epccs/RPUno/Hardware/Evaluation/RPUno^5+K3^1+RPUadpt^4_wValvesPvBat.jpg

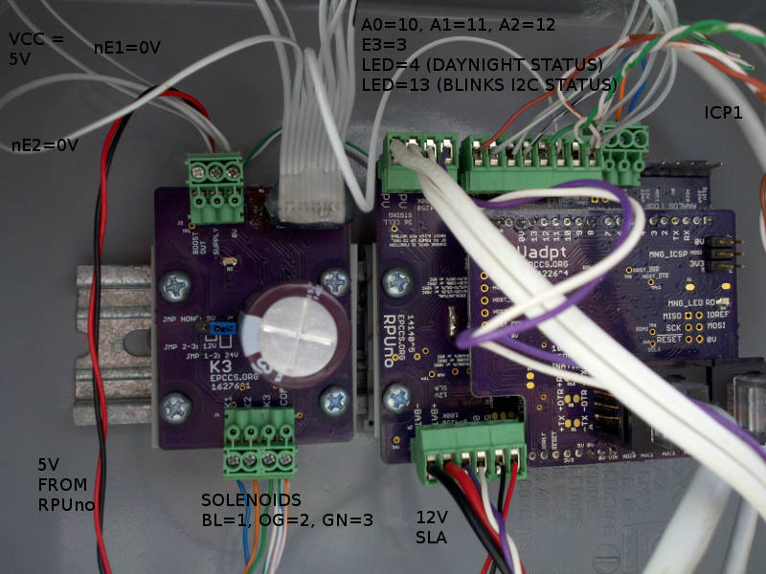
Hardware/Evaluation/RPUno^5+K3^1+RPUadpt^4_wValvesPvBat.jpg
