epccs/RPUno/Alternat/Setup/AuxilaryWiring.sch

## EAGLE design Alternat/Setup/AuxilaryWiring.sch (2018-12-21)

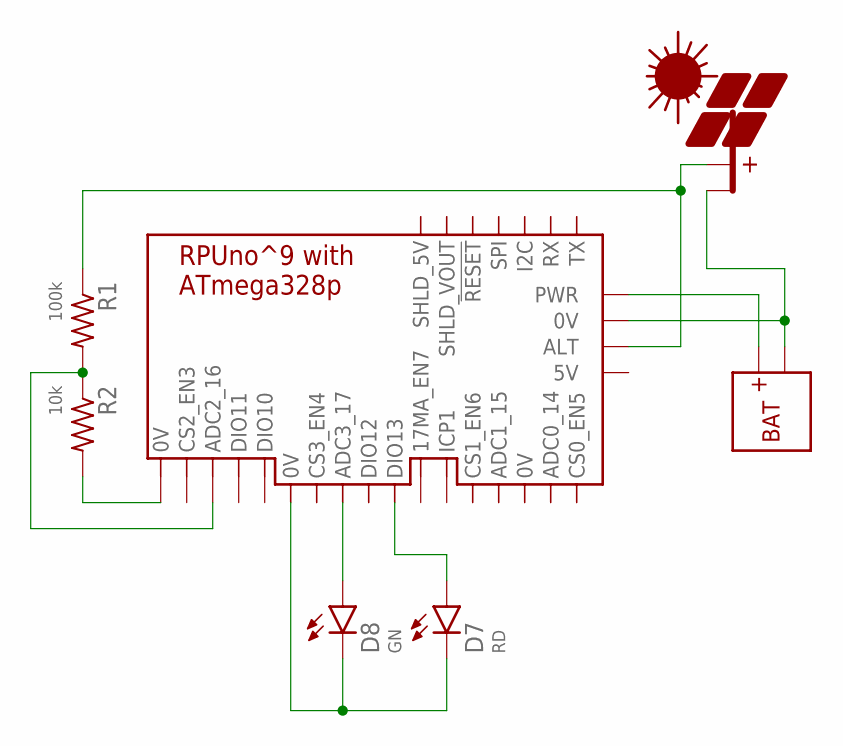
[picture p53: schematic AuxilaryWiring.sch]

Parts:
BM1: RPUNO; NA-30
D7: RD; LED5MM
D8: GN; LED5MM
PV4: PV; NA-30
R1: 100k; C0805(2012)
R2: 10k; C0805(2012)
U$7: BAT; NA-30

Connections:
unnamed: BM1.27 (0V), R2.2
unnamed: BM1.13 (ADC2_16), R1.2, R2.1
unnamed: BM1.18 (DIO13), D7.A
unnamed: BM1.28 (0V), D7.K, D8.K
unnamed: BM1.16 (ADC3_17), D8.A
unnamed: BM1.8 (PWR), U$7.1 (+BAT)
unnamed: BM1.9 (0V), PV4.2 (-PV), U$7.2 (-BAT)
unnamed: BM1.20 (ALT), PV4.1 (+PV), R1.1
