epccs/RPUno/DayNight/Setup/LightSensorWiring.sch

## EAGLE design DayNight/Setup/LightSensorWiring.sch (2018-12-10)

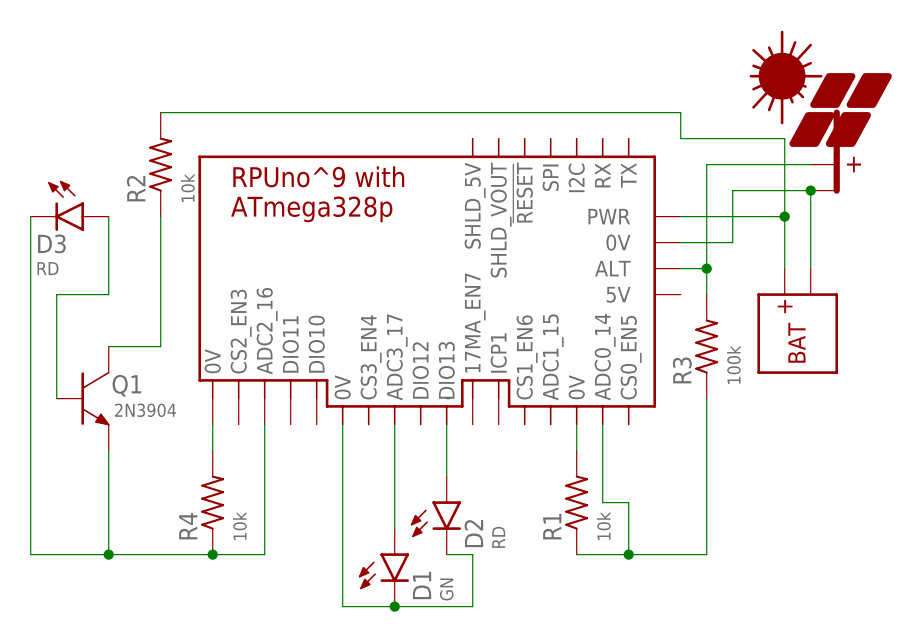
[picture p54: schematic LightSensorWiring.sch]

Parts:
BM1: RPUNO; NA-30
D1: GN; LED5MM
D2, D3: RD; LED5MM
PV4: PV; NA-30
Q1: 2N3904; SOT23
R1, R2, R4: 10k; C0805(2012)
R3: 100k; C0805(2012)
U$7: BAT; NA-30

Connections:
0V: BM1.9 (0V), PV4.2 (-PV), U$7.2 (-BAT)
unnamed: BM1.8 (PWR), R2.2, U$7.1 (+BAT)
unnamed: BM1.26 (0V), R1.2
unnamed: BM1.28 (0V), D1.K, D2.K
unnamed: D3.A, Q1.B
unnamed: BM1.13 (ADC2_16), D3.K, Q1.E, R4.1
unnamed: BM1.11 (ADC0_14), R1.1, R3.1
unnamed: Q1.C, R2.1
unnamed: BM1.27 (0V), R4.2
unnamed: BM1.18 (DIO13), D2.A
unnamed: BM1.16 (ADC3_17), D1.A
unnamed: BM1.20 (ALT), PV4.1 (+PV), R3.2
