epccs/RPUno/Hardware/Design/MultiDrop.sch

## EAGLE design Hardware/Design/MultiDrop.sch (2018-05-22)

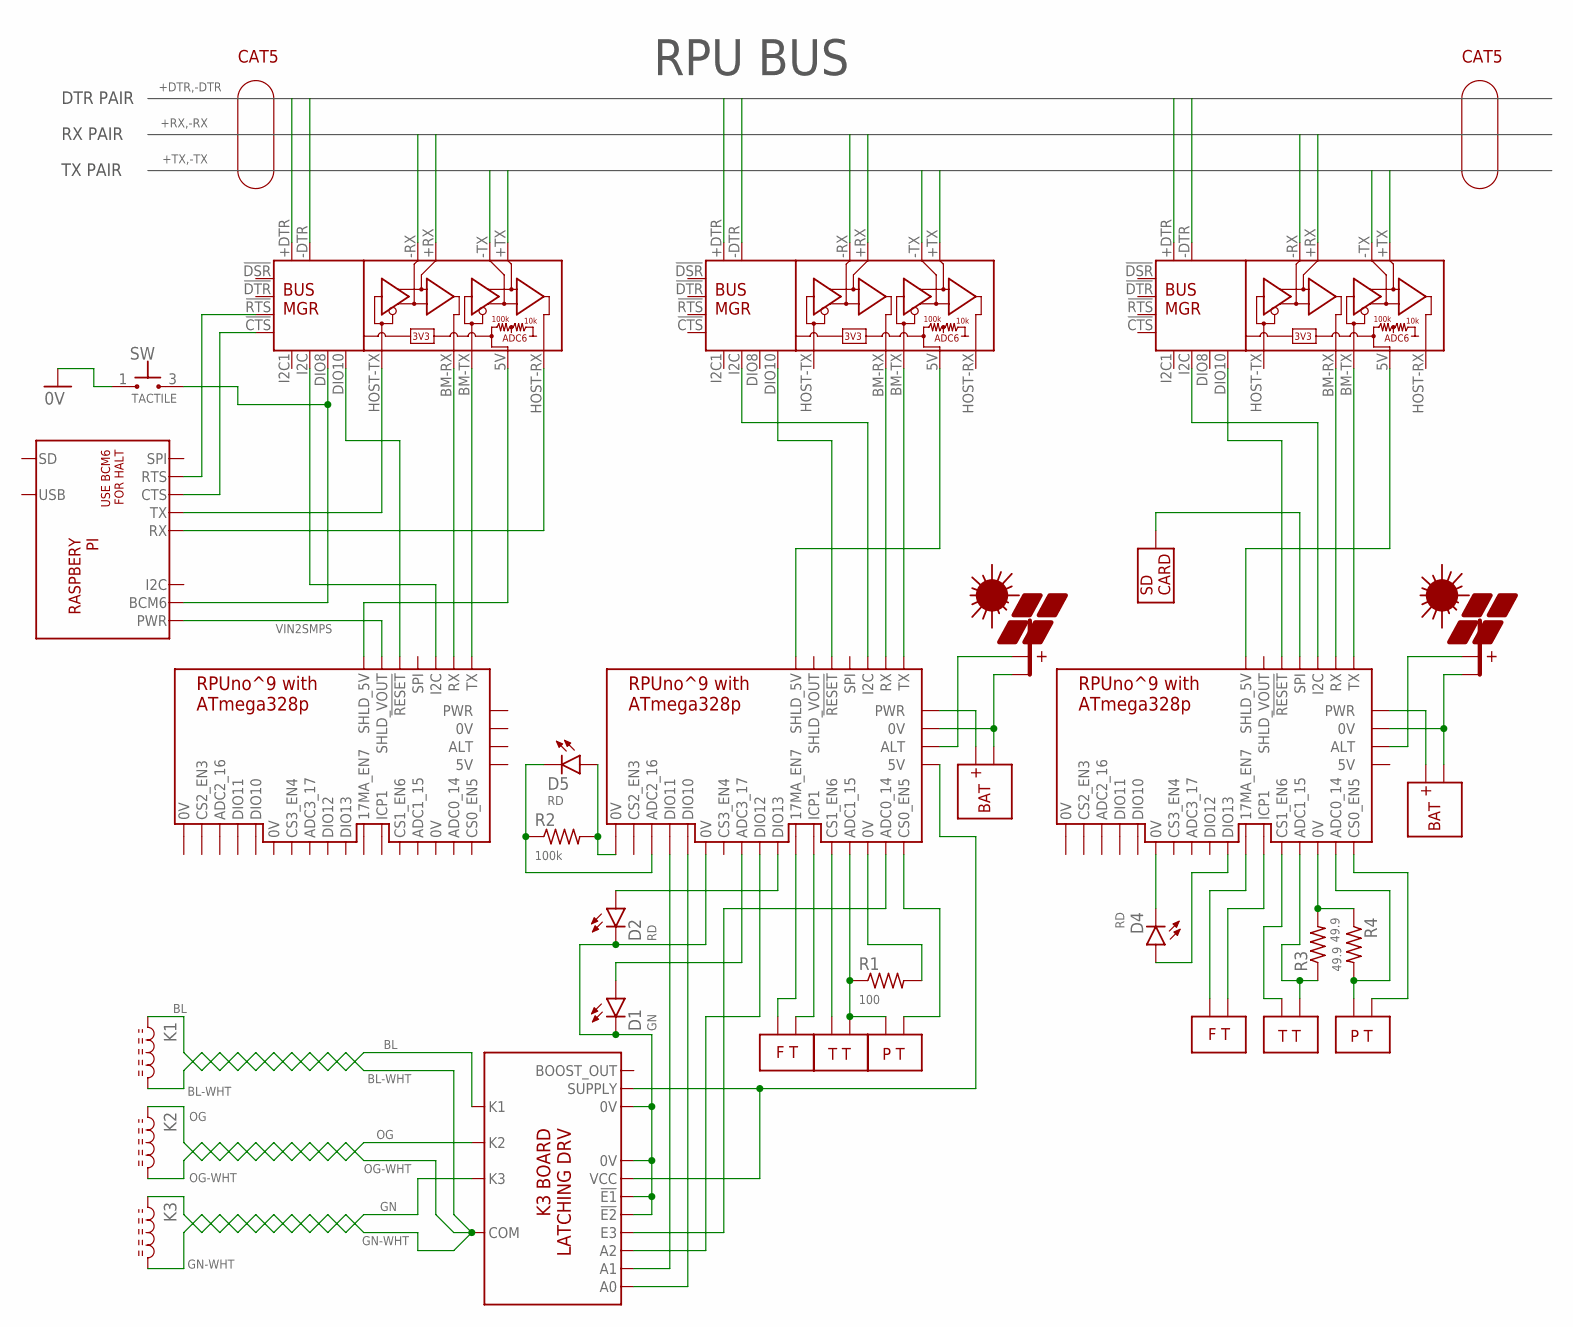
[picture p55: schematic MultiDrop.sch]

Parts:
BM1, BM2, BM3: RPUNO; NA-30
D1: GN; LED5MM
D2, D4, D5: RD; LED5MM
K1, K2, K3: L0805; C0805(2012)
PV2, PV4: PV; NA-30
R1: 100; C0805(2012)
R2: 100k; C0805(2012)
R3, R4: 49.9; C0805(2012)
SD2: SD; NA-30
SW: TACTILE; KS11
U$1, U$2, U$3: BUS_MGR; WITH_RPU_NAMES
U$4: K3; NA-30
U$5, U$12: FT; NA-30
U$6, U$10: TT; NA-30
U$7, U$9: BAT; NA-30
U$8, U$11: PT; NA-30
U$13: PI; NA-30

Connections:
0V: SW.1
+DTR: U$3.+DTR
+DTR1: U$2.+DTR
+DTR3: U$1.+DTR
+RX: U$3.+RX
+RX1: U$2.+RX
+RX3: U$1.+RX
+TX: U$3.+TX
+TX1: U$2.+TX
+TX3: U$1.+TX
-DTR: U$3.-DTR
-DTR1: U$2.-DTR
-DTR3: U$1.-DTR
-RX: U$3.-RX
-RX1: U$2.-RX
-RX3: U$1.-RX
-TX: U$3.-TX
-TX1: U$2.-TX
-TX3: U$1.-TX
BL: K1.1, U$4.11 (K1)
BL-WHT: K1.2, U$4.9 (COM)
GN: K3.1, U$4.13 (K3)
GN-WHT: K3.2
unnamed: BM2.1 (TX), U$3.BM-TX (BM_TX)
unnamed: BM2.2 (RX), U$3.BM-RX (BM_RX)
unnamed: SW.3, U$3.DIO8, U$13.7 (BCM6)
unnamed: U$3.!CTS, U$13.1 (CTS)
unnamed: U$3.!RTS, U$13.2 (RTS)
unnamed: BM1.27 (0V), D5.A, R2.2
unnamed: BM1.13 (ADC2_16), D5.K, R2.1
unnamed: U$3.HOST-RX (HOST_RX), U$13.3 (RX)
unnamed: U$3.HOST-TX (HOST_TX), U$13.4 (TX)
unnamed: BM1.1 (TX), U$2.BM-TX (BM_TX)
unnamed: BM1.2 (RX), U$2.BM-RX (BM_RX)
unnamed: BM1.9 (0V), PV2.2 (-PV), U$9.2 (-BAT)
unnamed: BM3.9 (0V), PV4.2 (-PV), U$7.2 (-BAT)
unnamed: BM3.1 (TX), U$1.BM-TX (BM_TX)
unnamed: BM3.20 (ALT), PV4.1 (+PV)
unnamed: BM3.8 (PWR), U$7.1 (+BAT)
unnamed: BM1.19 (5V), U$4.14 (SUPPLY), U$4.15 (VCC)
unnamed: BM3.26 (0V), R3.2, R4.1
unnamed: BM1.11 (ADC0_14), U$4.10 (E3)
unnamed: BM3.18 (DIO13), D4.A
unnamed: BM3.2 (RX), U$1.BM-RX (BM_RX)
unnamed: BM1.20 (ALT), PV2.1 (+PV)
unnamed: BM3.21 (17MA_EN7), U$12.2 (PWR)
unnamed: BM1.15 (DIO10), U$4.5 (A0)
unnamed: BM1.14 (DIO11), U$4.6 (A1)
unnamed: BM1.17 (DIO12), U$4.7 (A2)
unnamed: BM1.26 (0V), R1.2
unnamed: BM3.4 (SPI), SD2.1
unnamed: BM2.6 (SHLD_5V), U$3.5V (PWR)
unnamed: BM2.5 (!RESET), U$3.DIO10
unnamed: BM3.10 (ADC1_15), R3.1, U$10.1 (4TO20)
unnamed: BM3.3 (I2C), U$1.I2C
unnamed: BM2.3 (I2C), U$3.I2C
unnamed: BM3.22 (CS1_EN6), U$10.2 (PWR)
unnamed: BM3.12 (ICP1), U$12.1 (PL)
unnamed: BM1.18 (DIO13), D2.A
unnamed: BM1.16 (ADC3_17), D1.A
unnamed: BM3.11 (ADC0_14), R4.2, U$8.2 (PWR)
unnamed: BM3.23 (CS0_EN5), U$8.1 (4TO20)
unnamed: BM1.28 (0V), D1.K, D2.K, U$4.1 (!E1), U$4.2 (!E2), U$4.3 (0V), U$4.4 (0V)
unnamed: BM3.6 (SHLD_5V), U$1.5V (PWR)
unnamed: BM1.8 (PWR), U$9.1 (+BAT)
unnamed: BM3.5 (!RESET), U$1.DIO10
unnamed: BM1.5 (!RESET), U$2.DIO10
unnamed: BM1.6 (SHLD_5V), U$2.5V (PWR)
unnamed: BM1.21 (17MA_EN7), U$5.2 (PWR)
unnamed: BM1.3 (I2C), U$2.I2C
unnamed: BM1.12 (ICP1), U$5.1 (PL)
unnamed: BM1.22 (CS1_EN6), U$6.2 (PWR)
unnamed: BM1.10 (ADC1_15), R1.1, U$6.1 (4TO20), U$11.2 (PWR)
unnamed: BM1.23 (CS0_EN5), U$11.1 (4TO20)
unnamed: BM3.28 (0V), D4.K
OG: K2.1, U$4.12 (K2)
OG-WHT: K2.2
VIN2SMPS: BM2.7 (SHLD_VOUT), U$13.12 (PWR)

Notes on the sheet:
CAT5
DTR PAIR
RX PAIR
TX PAIR
RPU BUS
