epccs/RPUno/KNL/Setup/KNLWiring.sch

## EAGLE design KNL/Setup/KNLWiring.sch (2018-06-09)

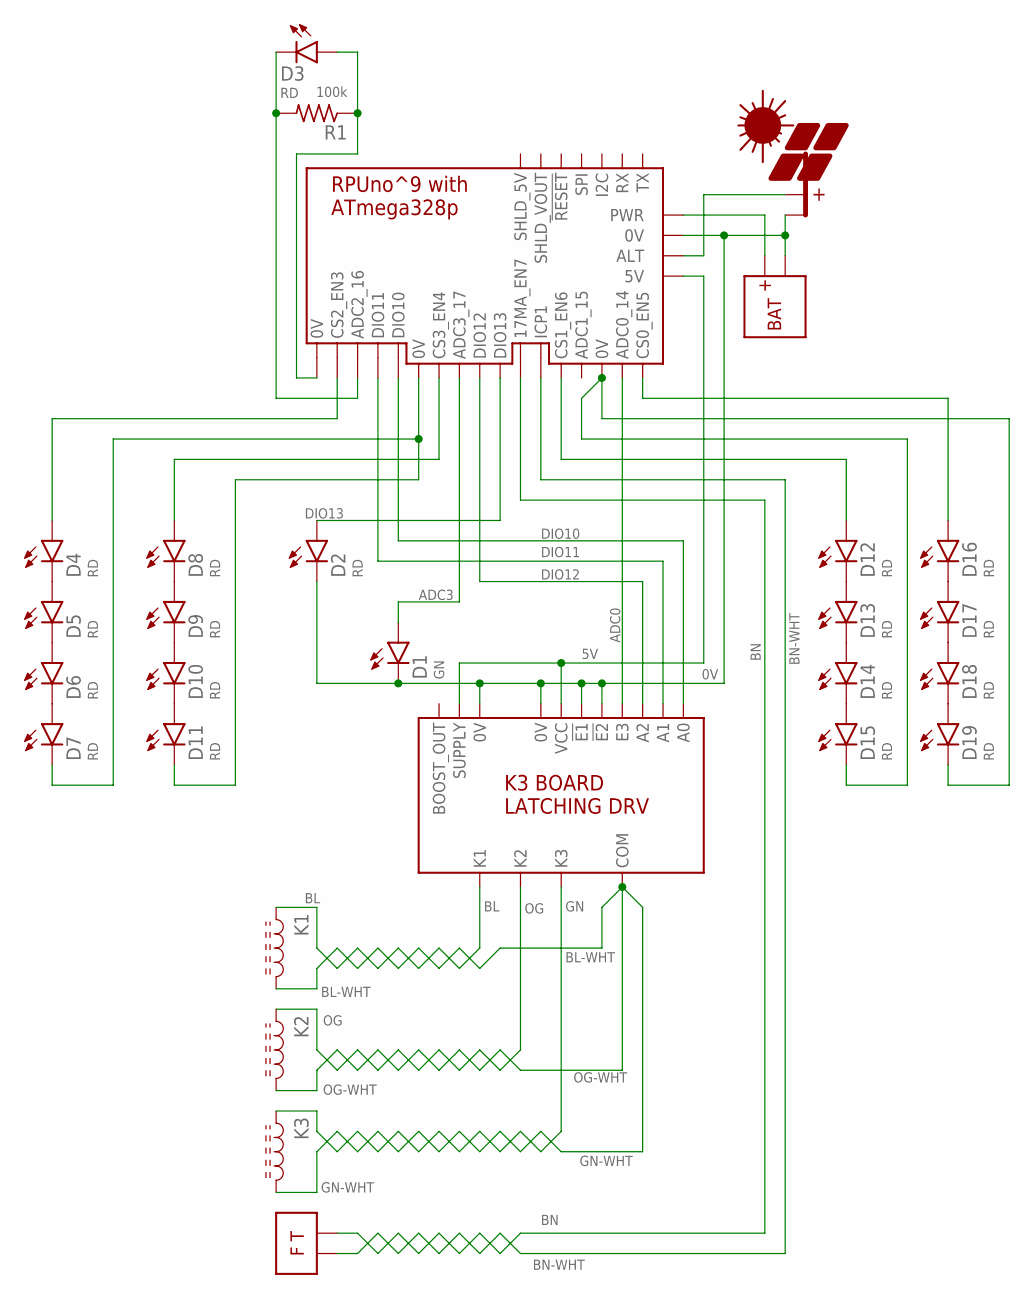
[picture p56: schematic KNLWiring.sch]

Parts:
BM1: RPUNO; NA-30
D1: GN; LED5MM
D2, D3, D4, D5, D6, D7, D8, D9, D10, D11, D12, D13, D14, D15, D16, D17, D18, D19: RD; LED5MM
K1, K2, K3: L0805; C0805(2012)
PV4: PV; NA-30
R1: 100k; C0805(2012)
U$1: K3; NA-30
U$2: FT; NA-30
U$7: BAT; NA-30

Connections:
0V: BM1.9 (0V), D1.K, D2.K, PV4.2 (-PV), U$1.1 (!E1), U$1.2 (!E2), U$1.3 (0V), U$1.4 (0V), U$7.2 (-BAT)
5V: BM1.19 (5V), U$1.14 (SUPPLY), U$1.15 (VCC)
ADC0: BM1.11 (ADC0_14), U$1.10 (E3)
ADC3: BM1.16 (ADC3_17), D1.A
BL: K1.1, U$1.11 (K1)
BL-WHT: K1.2, U$1.9 (COM)
BN: BM1.21 (17MA_EN7), U$2.2 (PWR)
BN-WHT: BM1.12 (ICP1), U$2.1 (PL)
DIO10: BM1.15 (DIO10), U$1.5 (A0)
DIO11: BM1.14 (DIO11), U$1.6 (A1)
DIO12: BM1.17 (DIO12), U$1.7 (A2)
DIO13: BM1.18 (DIO13), D2.A
GN: K3.1, U$1.13 (K3)
GN-WHT: K3.2
unnamed: BM1.8 (PWR), U$7.1 (+BAT)
unnamed: BM1.27 (0V), D3.A, R1.1
unnamed: BM1.13 (ADC2_16), D3.K, R1.2
unnamed: D4.K, D5.A
unnamed: D5.K, D6.A
unnamed: D6.K, D7.A
unnamed: BM1.24 (CS2_EN3), D4.A
unnamed: D8.K, D9.A
unnamed: D9.K, D10.A
unnamed: D10.K, D11.A
unnamed: BM1.29 (CS3_EN4), D8.A
unnamed: D13.K, D14.A
unnamed: BM1.28 (0V), D7.K, D11.K
unnamed: D14.K, D15.A
unnamed: D16.K, D17.A
unnamed: D17.K, D18.A
unnamed: D18.K, D19.A
unnamed: D12.K, D13.A
unnamed: BM1.22 (CS1_EN6), D12.A
unnamed: BM1.23 (CS0_EN5), D16.A
unnamed: BM1.26 (0V), D15.K, D19.K
unnamed: BM1.20 (ALT), PV4.1 (+PV)
OG: K2.1, U$1.12 (K2)
OG-WHT: K2.2
