epccs/RPUno/NightLight/Setup/NightLightWiring.sch

## EAGLE design NightLight/Setup/NightLightWiring.sch (2018-06-03)

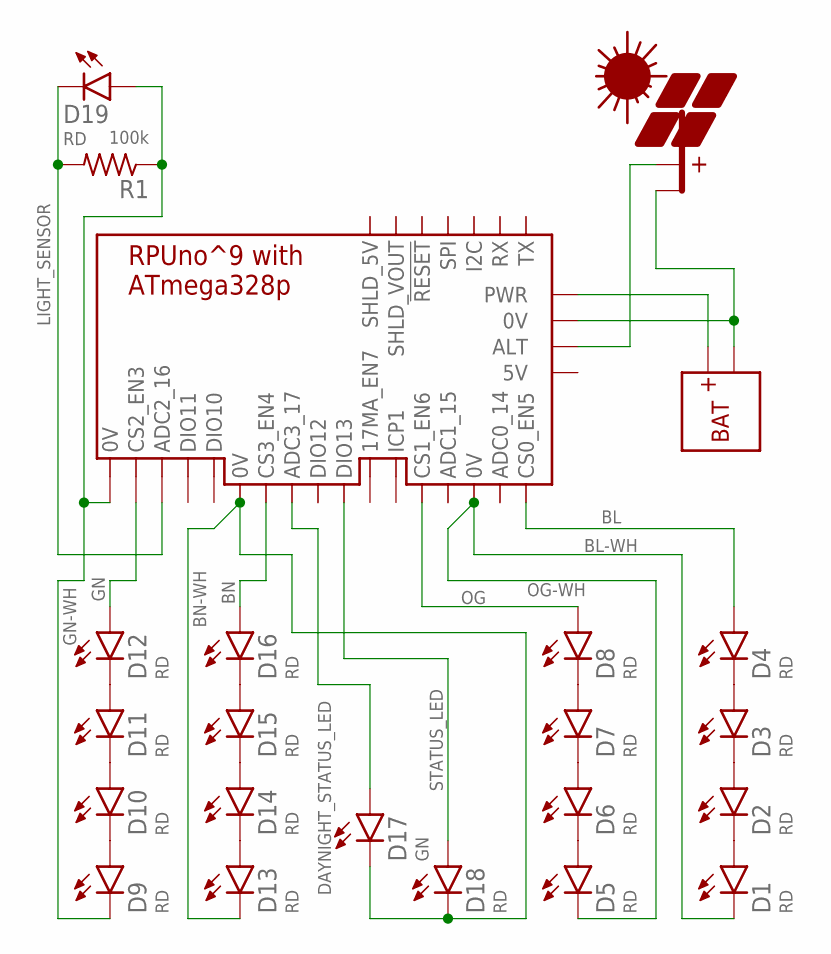
[picture p57: schematic NightLightWiring.sch]

Parts:
BM3: RPUNO; NA-30
D1, D2, D3, D4, D5, D6, D7, D8, D9, D10, D11, D12, D13, D14, D15, D16, D18, D19: RD; LED5MM
D17: GN; LED5MM
PV4: PV; NA-30
R1: 100k; C0805(2012)
U$7: BAT; NA-30

Connections:
0V: D17.K, D18.K
BL: BM3.23 (CS0_EN5), D4.A
BL-WH: BM3.26 (0V), D1.K
BN: BM3.29 (CS3_EN4), D16.A
BN-WH: BM3.28 (0V), D13.K
DAYNIGHT_STATUS_LED: BM3.16 (ADC3_17), D17.A
GN: BM3.24 (CS2_EN3), D12.A
GN-WH: BM3.27 (0V), D9.K, D19.A, R1.1
LIGHT_SENSOR: BM3.13 (ADC2_16), D19.K, R1.2
unnamed: D2.A, D3.K
unnamed: D3.A, D4.K
unnamed: D1.A, D2.K
unnamed: D5.A, D6.K
unnamed: D6.A, D7.K
unnamed: D7.A, D8.K
unnamed: D9.A, D10.K
unnamed: D10.A, D11.K
unnamed: D11.A, D12.K
unnamed: D13.A, D14.K
unnamed: D14.A, D15.K
unnamed: D15.A, D16.K
unnamed: PV4.2 (-PV), U$7.2 (-BAT)
OG: BM3.22 (CS1_EN6), D8.A
OG-WH: D5.K
STATUS_LED: BM3.18 (DIO13), D18.A
