epccs/RPUno/Reflow/Setup/ReflowWiring.sch

## EAGLE design Reflow/Setup/ReflowWiring.sch (2018-05-17)

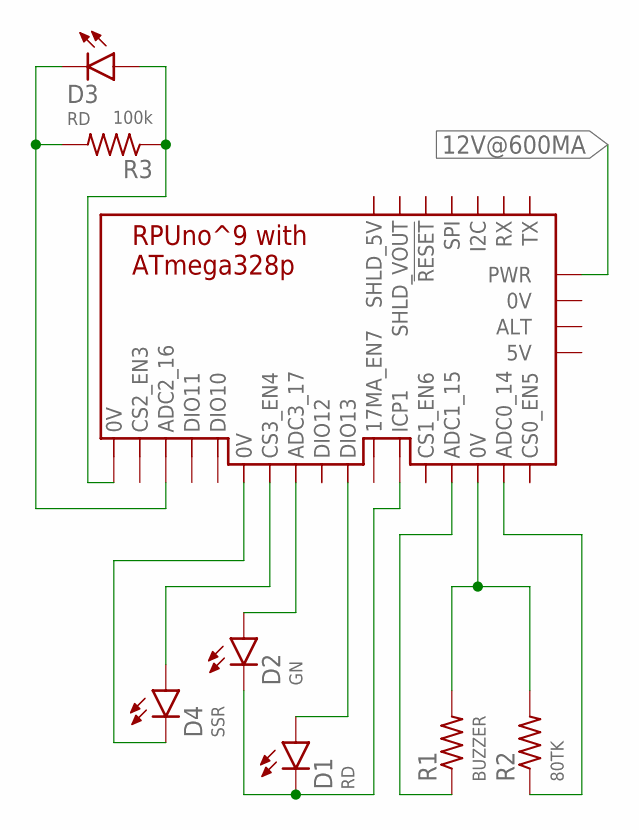
[picture p58: schematic ReflowWiring.sch]

Parts:
BM1: RPUNO; NA-30
D1, D3: RD; LED5MM
D2: GN; LED5MM
D4: SSR; LED5MM
R1: BUZZER; C0805(2012)
R2: 80TK; C0805(2012)
R3: 100k; C0805(2012)

Connections:
12V@600MA: BM1.8 (PWR)
DIO13: BM1.18 (DIO13), D1.A
unnamed: BM1.16 (ADC3_17), D2.A
unnamed: BM1.12 (ICP1), D1.K, D2.K
unnamed: BM1.29 (CS3_EN4), D4.A
unnamed: BM1.26 (0V), R1.2, R2.2
unnamed: BM1.28 (0V), D4.K
unnamed: BM1.10 (ADC1_15), R1.1
unnamed: BM1.11 (ADC0_14), R2.1
unnamed: BM1.27 (0V), D3.A, R3.1
unnamed: BM1.13 (ADC2_16), D3.K, R3.2
