epccs/RPUno/SelfTest/Setup/SelfTestWiring.sch

## EAGLE design SelfTest/Setup/SelfTestWiring.sch (2018-04-24)

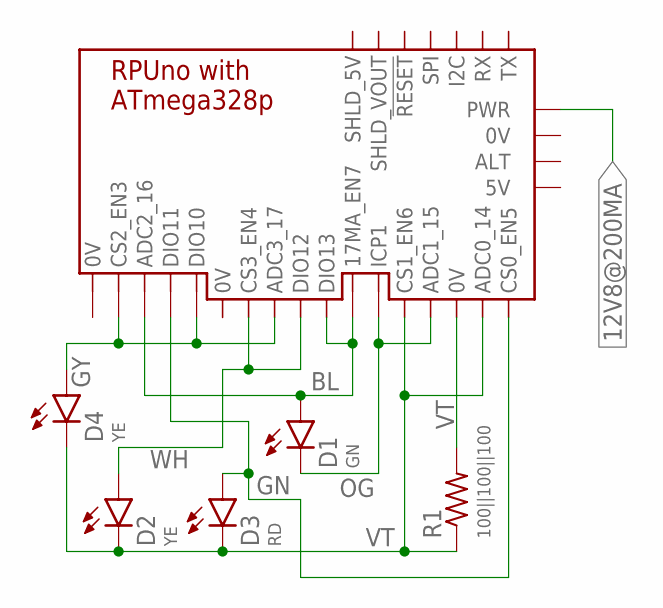
[picture p59: schematic SelfTestWiring.sch]

Parts:
BM3: RPUNO; NA-30
D1: GN; LED5MM
D2, D4: YE; LED5MM
D3: RD; LED5MM
R1: 100||100||100; C0805(2012)

Connections:
12V8@200MA: BM3.8 (PWR)
BL: BM3.13 (ADC2_16), BM3.18 (DIO13), BM3.21 (17MA_EN7), D1.A
GN: BM3.14 (DIO11), BM3.23 (CS0_EN5), D3.A
GY: BM3.15 (DIO10), BM3.16 (ADC3_17), BM3.24 (CS2_EN3), D4.A
unnamed: BM3.26 (0V), R1.2
OG: BM3.10 (ADC1_15), BM3.12 (ICP1), D1.K
VT: BM3.11 (ADC0_14), BM3.22 (CS1_EN6), D2.K, D3.K, D4.K, R1.1
WH: BM3.17 (DIO12), BM3.29 (CS3_EN4), D2.A
