epccs/RPUno/SpiSlv/Setup/SpiSlvWiring.sch

## EAGLE design SpiSlv/Setup/SpiSlvWiring.sch (2019-03-19)

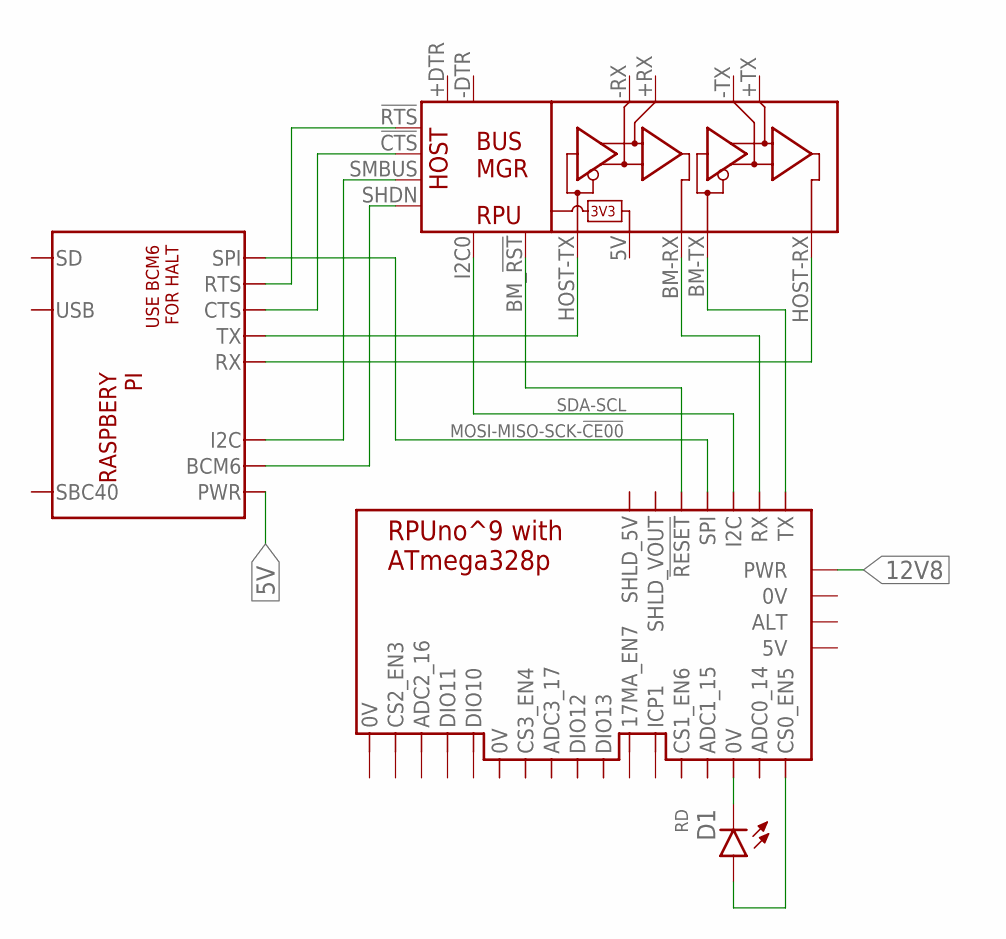
[picture p61: schematic SpiSlvWiring.sch]

Parts:
BM1: RPUNO; NA-30
D1: RD; LED5MM
U$1: PI; NA-30
U$2: BUS_MGR; WITH_RPU_NAMES

Connections:
5V: U$1.12 (PWR)
12V8: BM1.8 (PWR)
MOSI-MISO-SCK-!CE00: BM1.4 (SPI), U$1.10 (SPI)
unnamed: BM1.23 (CS0_EN5), D1.A
unnamed: BM1.26 (0V), D1.K
unnamed: U$1.1 (CTS), U$2.!CTS
unnamed: U$1.2 (RTS), U$2.!RTS
unnamed: BM1.2 (RX), U$2.BM-RX (BM_RX)
unnamed: U$1.3 (RX), U$2.HOST-RX (HOST_RX)
unnamed: U$1.4 (TX), U$2.HOST-TX (HOST_TX)
unnamed: BM1.1 (TX), U$2.BM-TX (BM_TX)
unnamed: U$1.8 (I2C), U$2.SMBUS
unnamed: U$1.7 (BCM6), U$2.SHDN
SDA-SCL: BM1.3 (I2C), U$2.I2C0
THRU-74LVC07: BM1.5 (!RESET), U$2.BM_!RST! (BM-!RST!)
