epccs/RPUno/XcvrTest/Setup/XcvrTestWiring.sch

## EAGLE design XcvrTest/Setup/XcvrTestWiring.sch (2019-06-23)

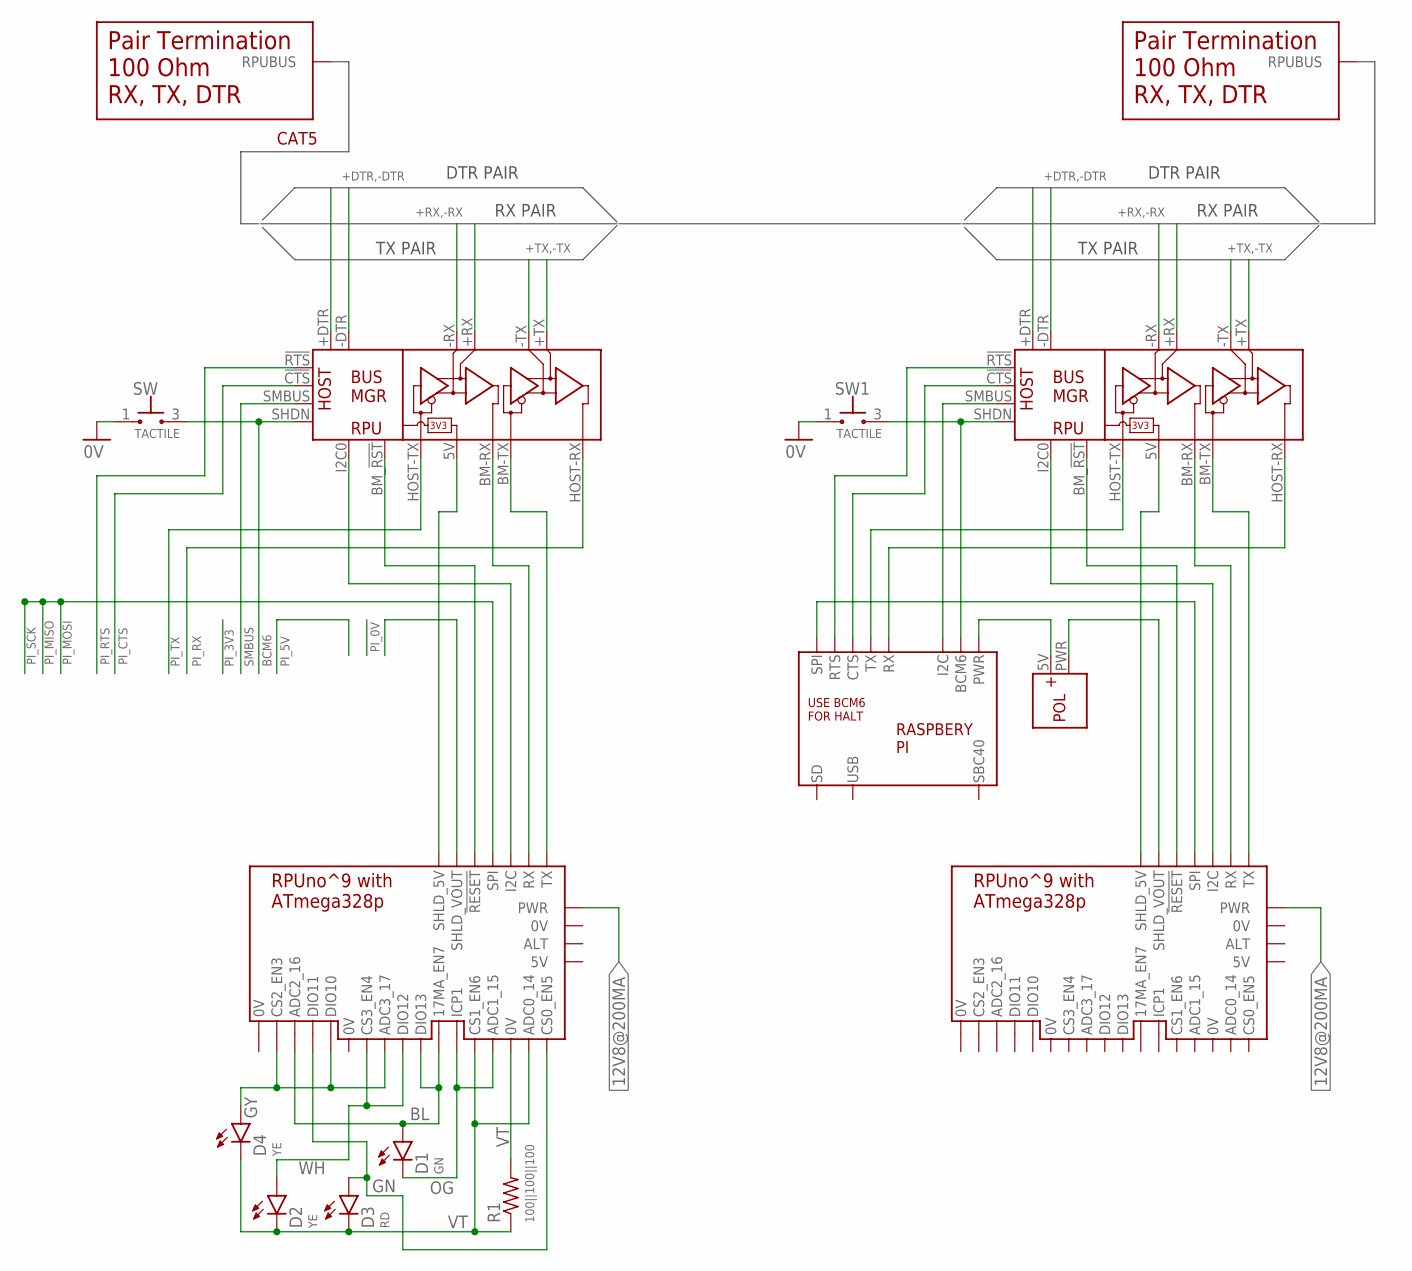
[picture p62: schematic XcvrTestWiring.sch]

Parts:
BM1, BM3: RPUNO; NA-30
D1: GN; LED5MM
D2, D4: YE; LED5MM
D3: RD; LED5MM
R1: 100||100||100; C0805(2012)
SW, SW1: TACTILE; KS11
U$1, U$3: TERM; NA-30
U$2, U$8: BUS_MGR; WITH_RPU_NAMES
U$4: PI; NA-30
U$5: POL; WITH_RPU_NAMES

Connections:
0V: SW.1, SW1.1
12V8@200MA: BM1.8 (PWR), BM3.8 (PWR)
+DTR: U$2.+DTR, U$8.+DTR
+RX: U$2.+RX, U$8.+RX
+TX: U$2.+TX, U$8.+TX
-DTR: U$2.-DTR, U$8.-DTR
-RX: U$2.-RX, U$8.-RX
-TX: U$2.-TX, U$8.-TX
BCM6: SW.3, SW1.3, U$2.SHDN, U$4.7 (BCM6), U$8.SHDN
BL: BM3.13 (ADC2_16), BM3.18 (DIO13), BM3.21 (17MA_EN7), D1.A
GN: BM3.14 (DIO11), BM3.23 (CS0_EN5), D3.A
GY: BM3.15 (DIO10), BM3.16 (ADC3_17), BM3.24 (CS2_EN3), D4.A
unnamed: BM3.26 (0V), R1.2
unnamed: BM3.1 (TX), U$8.BM-TX (BM_TX)
unnamed: BM3.2 (RX), U$8.BM-RX (BM_RX)
unnamed: BM1.1 (TX), U$2.BM-TX (BM_TX)
unnamed: BM1.2 (RX), U$2.BM-RX (BM_RX)
unnamed: BM1.6 (SHLD_5V), U$2.5V (PWR)
unnamed: BM1.5 (!RESET), U$2.BM_!RST! (BM-!RST!)
unnamed: BM1.3 (I2C), U$2.I2C0
unnamed: BM1.7 (SHLD_VOUT), U$5.PWR (VIN)
unnamed: BM3.6 (SHLD_5V), U$8.5V (PWR)
unnamed: BM3.5 (!RESET), U$8.BM_!RST! (BM-!RST!)
unnamed: BM3.3 (I2C), U$8.I2C0
OG: BM3.10 (ADC1_15), BM3.12 (ICP1), D1.K
PI_5V: U$4.12 (PWR), U$5.5V
PI_CTS: U$2.!CTS, U$4.1 (CTS), U$8.!CTS
PI_MOSI: BM1.4 (SPI), BM3.4 (SPI), U$4.10 (SPI)
PI_RTS: U$2.!RTS, U$4.2 (RTS), U$8.!RTS
PI_RX: U$2.HOST-RX (HOST_RX), U$4.3 (RX), U$8.HOST-RX (HOST_RX)
PI_TX: U$2.HOST-TX (HOST_TX), U$4.4 (TX), U$8.HOST-TX (HOST_TX)
SMBUS: U$2.SMBUS, U$4.8 (I2C), U$8.SMBUS
VT: BM3.11 (ADC0_14), BM3.22 (CS1_EN6), D2.K, D3.K, D4.K, R1.1
WH: BM3.17 (DIO12), BM3.29 (CS3_EN4), D2.A

Notes on the sheet:
CAT5
DTR PAIR
RX PAIR
TX PAIR
