epccs/RPUno/Capture/capture.c

/*
capture  is a library that returns the ICP1 timing counts for its ICP events
Copyright (C) 2019 Ronald Sutherland

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
  You should have received a copy of the GNU Lesser General Public
  License along with this library; if not, write to the Free Software
  Foundation, Inc., 51 Franklin St, Fifth Floor, Boston, MA  02110-1301  USA
*/
#include <avr/pgmspace.h>
#include <util/atomic.h>
#include <stdio.h>
#include <stdlib.h> 
#include "../lib/parse.h"
#include "../lib/icp_buf.h"
#include "../lib/icp1.h"
#include "../lib/timers.h"
#include "capture.h"

#define SERIAL_PRINT_DELAY_MILSEC 60000
static unsigned long serial_print_started_at;

static uint16_t low;
static uint16_t high;

// a double buffer of the event capture is used for serial output
ICP icp1_db;

static int event_pair;
static int event_pair_output;
static uint8_t event_pair_status;

static int event_report;
static int event_report_output;
static uint8_t event_report_status; 

/* event count of ICP1 
    no artuments needed*/
void Count(void)
{
    if ( (command_done == 10) )
    {
        serial_print_started_at = millis();
        // the count must not change while reading chCount
        uint32_t local_cpy_icp1_event_count;
        ATOMIC_BLOCK ( ATOMIC_RESTORESTATE )
        {
            local_cpy_icp1_event_count = icp1.count;
        }
        printf_P(PSTR("{\"icp1\":{\"count\":\"%lu\"}}\r\n"),local_cpy_icp1_event_count);
        command_done = 11;
    }
    else if ( (command_done == 11) )
    { // delay between JSON printing
        unsigned long kRuntime= millis() - serial_print_started_at;
        if ((kRuntime) > ((unsigned long)SERIAL_PRINT_DELAY_MILSEC))
        {
            command_done = 10; /* This keeps looping the output forever (until a Rx char anyway) */
        }
    }
    else
    {
        initCommandBuffer();
    }
}

/* return ICP1 timer count for both low and high signal timing.
    Low value is the counts between a falling edge and a rising edge.
    High value is the counts between a rising edge and falling edge.
    The ratio may be used to determine the duty.*/
void Capture(void)
{
    if ( icp1_edge_mode != TRACK_BOTH)
    {
        printf_P(PSTR("{\"err\":\"IcpWrongMode\"}\r\n"));
        initCommandBuffer();
        return;
    }
    if ( (command_done == 10) )
    {
        if (arg_count == 0)
        {
            event_pair = 1;
        }
        else if (arg_count == 2)
        { // arg[0] should say icp1, other mcu's may have icp3...
            event_pair = atoi(arg[1]);
        }
        else
        {
            printf_P(PSTR("{\"err\":\"IcpArgCnt@%d!=0|2\"}\r\n"),arg_count);
            initCommandBuffer();   
        }

        if ((event_pair < 1) || (event_pair >= (ICP_EVENT_BUFF_SIZE/2)) )
        {
            printf_P(PSTR("{\"err\":\"IcpMaxArg%d\"}\r\n"),(ICP_EVENT_BUFF_SIZE/2)-1);
            initCommandBuffer();
        }
        else
        {
            // event_pair should have a valid value for how many high-low capture pairs to print, but I need a counter to track up to it.
            event_pair_output =0;
            
            // buffer has enough readings
            if (icp1.count > ((event_pair * 2) +1) ) 
            { 
                uint8_t num_of_events_needed=((event_pair * 2) +1);
                
                // copy from icp1 to icp1_db
                double_buffer_copy(&icp1, &icp1_db, num_of_events_needed);
                
                // used to delay serial printing
                serial_print_started_at = millis();
                
                command_done = 11;
            }
            else
            {
                printf_P(PSTR("{\"err\":\"IcpEvntCnt@%d\"}\r\n"), icp1.count);
                initCommandBuffer();
            }
        }
    }
    else if ( (command_done == 11) )
    { // use the event_count for indexing the time stamps
        printf_P(PSTR("{\"icp1\":{\"count\":\"%lu\","),(icp1_db.count - 2*(event_pair_output) ) );
        command_done = 12;
    }

    else if ( (command_done == 12) )
    {
        // cast to int to use two's complement math then cast back into a uint8_t and mask to the buffer size.
        uint8_t high2low_event_index = ((uint8_t)(((int8_t)icp1_db.head) - ((int8_t)2*(event_pair_output)))) & (ICP_EVENT_BUFF_MASK);
        uint8_t low2high_event_index = ((uint8_t)(((int8_t)high2low_event_index) - 1)) & (ICP_EVENT_BUFF_MASK);
        uint8_t period_event_index = ((uint8_t)(((int8_t)low2high_event_index) - 1)) & (ICP_EVENT_BUFF_MASK);

        // the event time is keep in two byte arrays to make the ISR fast and 
        // allow up to 32 events with quick access of the AVR ldd instruction.
        uint16_t high2low_event;
        uint16_t low2high_event;
        uint16_t period_event;
        high2low_event = (((uint16_t)icp1_db.event.Byt1[high2low_event_index]) <<8) + ((uint16_t)icp1_db.event.Byt0[high2low_event_index]);
        low2high_event = (((uint16_t)icp1_db.event.Byt1[low2high_event_index]) <<8) + ((uint16_t)icp1_db.event.Byt0[low2high_event_index]);
        period_event = (((uint16_t)icp1_db.event.Byt1[period_event_index]) <<8) + ((uint16_t)icp1_db.event.Byt0[period_event_index]);

        // Now find counts between events while ICP1 was low and then when it was high
        // cast to int causes two's complement math to be used which gives correct result through a roll over
        low = (uint16_t)((int16_t)high2low_event - (int16_t)low2high_event);
        high = (uint16_t)((int16_t)low2high_event - (int16_t)period_event);
        
        // if the last capture was on a falling event, swap low and high count
        if ( (icp1_db.event.status[high2low_event_index] & (1<<RISING)) == 0)
        { 
            uint16_t temp = low;
            low = high;
            high = temp;
        }
        
        // status of the three events are combined... only the most recent RISING flag is given 
        // bit 0 has RISING status bit from  high2low_event_index 
        event_pair_status = (icp1_db.event.status[high2low_event_index] & (0x1)) ;
        
        // print in  steps otherwise the buffer will fill and block the program from running
        printf_P(PSTR("\"low\":\"%u\","),(unsigned int)low);
        command_done = 13;
    }
    else if ( (command_done == 13) )
    {
        printf_P(PSTR("\"high\":\"%u\","),(unsigned int)high);
        command_done = 14;
    }
    else if ( (command_done == 14) )
    {
        printf_P(PSTR("\"status\":\"%u\"}}\r\n"),(unsigned int)event_pair_status);
        if ( (++event_pair_output) >= event_pair) 
        {
            command_done = 15;
        }
        else
        {
            command_done = 11;
        }
    }
    else if ( (command_done == 15) )
    { // delay between JSON printing
        unsigned long kRuntime= millis() - serial_print_started_at;
        if ((kRuntime) > ((unsigned long)SERIAL_PRINT_DELAY_MILSEC))
        {
            command_done = 10; /* This keeps looping the output forever (until a Rx char anyway) */
        }
    }
    else
    {
        initCommandBuffer();
    }
}

/* return ICP1 timer count for each event and the timer value.
    Event value is an unsigned 32 bit count at the time of the event.*/
void Event(void)
{
    if ( (command_done == 10) )
    {
        if (arg_count == 0)
        {
            event_report = 1;
        }
        else if (arg_count == 2)
        { // arg[0] should say icp1, other mcu's may have icp3...
            event_report = atoi(arg[1]);
        }
        else
        {
            printf_P(PSTR("{\"err\":\"IcpArgCnt@%d!=0|2\"}\r\n"),arg_count);
            initCommandBuffer();   
        }

        if ((event_report < 1) || (event_report >= (ICP_EVENT_BUFF_SIZE)) )
        {
            printf_P(PSTR("{\"err\":\"IcpMaxEvents@%d\"}\r\n"),(ICP_EVENT_BUFF_SIZE-1));
            initCommandBuffer();
        }
        else
        {
            // event_pair should have a valid value for how many high-low capture pairs to print, but I need a counter to track up to it.
            event_report_output =0;
            
            // buffer has enough readings
            if (icp1.count > event_report) 
            { 
                // copy from icp1 to icp1_db
                double_buffer_copy(&icp1, &icp1_db, (uint8_t)event_report);
                
                // used to delay serial printing
                serial_print_started_at = millis();
                
                command_done = 11;
            }
            else
            {
                printf_P(PSTR("{\"err\":\"IcpEvntCnt@%d\"}\r\n"), icp1.count);
                initCommandBuffer();
            }
        }
    }
    else if ( (command_done == 11) )
    { // use the event_count for indexing the time stamps
        printf_P(PSTR("{\"icp1\":{\"count\":\"%lu\","),(icp1_db.count - event_report_output) );
        command_done = 12;
    }

    else if ( (command_done == 12) )
    {
        // cast to int to use two's complement math then cast back into a uint8_t and mask to the buffer size.
        uint8_t event_index = ( (uint8_t)(((int8_t)icp1_db.head) - ((int8_t)(event_report_output))) ) & (ICP_EVENT_BUFF_MASK);

        // the event time is keep in two byte arrays to make the ISR fast and 
        // allow up to 32 events with quick access of the AVR ldd instruction.
        uint16_t uint16_event;
        uint16_event = (((uint16_t)icp1_db.event.Byt1[event_index]) <<8) + ((uint16_t)icp1_db.event.Byt0[event_index]);

        event_report_status = icp1_db.event.status[event_index] ;

        // print in  steps otherwise the buffer will fill and block the program from running
        printf_P(PSTR("\"event\":\"%u\","),(unsigned int)uint16_event);
        command_done = 13;
    }
    else if ( (command_done == 13) )
    {
        printf_P(PSTR("\"status\":\"%u\"}}\r\n"),(unsigned int)event_report_status);
        if ( (++event_report_output) >= event_report) 
        {
            command_done = 14;
        }
        else
        {
            command_done = 11;
        }
    }
    else if ( (command_done == 14) )
    { // delay between JSON printing
        unsigned long kRuntime= millis() - serial_print_started_at;
        if ((kRuntime) > ((unsigned long)SERIAL_PRINT_DELAY_MILSEC))
        {
            command_done = 10; /* This keeps looping the output forever (until a Rx char anyway) */
        }
    }
    else
    {
        initCommandBuffer();
    }
}

void InitICP(void)
{
     if ( (command_done == 10) )
    {
        // call with arg[0] == icp1 and three arguments
        int prescale = atoi(arg[2]);

        if ((prescale < 0) || (prescale > 0x5) )
        {
            printf_P(PSTR("{\"err\":\"IcpPrescalBad\"}\r\n"));
            initCommandBuffer();
        }
        
        if ( !( (strcmp_P( arg[1], PSTR("rise")) == 0) | 
                 (strcmp_P( arg[1], PSTR("fall")) == 0) | 
                 (strcmp_P( arg[1], PSTR("both")) == 0) ) )
       {
            printf_P(PSTR("{\"err\":\"IcpRiseFallBoth\"}\r\n"));
            initCommandBuffer();
        }
        printf_P(PSTR("{\"icp1\":{\"edgSel\":\"%s\","),arg[1]);
        command_done = 11;
    }
    else if ( (command_done == 11) )
    { 
        uint8_t prescale;
        prescale = (uint8_t)(atoi(arg[2]) & 0x7);
        if (strcmp_P( arg[1], PSTR("rise")) == 0)
        {
            initIcp1(TRACK_RISING, prescale) ;
        }
        if (strcmp_P( arg[1], PSTR("fall")) == 0)
        {
            initIcp1(TRACK_FALLING, prescale) ;
        }
        if (strcmp_P( arg[1], PSTR("both")) == 0)
        {
            initIcp1(TRACK_BOTH, prescale) ;
        }
        printf_P(PSTR("\"preScalr\":\"%d\"}}\r\n"),prescale);
        initCommandBuffer();
    }
}
