epccs/RPUno/Digital/digital.c

/*
digital is a library with Wiring like functions
Copyright (C) 2019 Ronald Sutherland

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
  You should have received a copy of the GNU Lesser General Public
  License along with this library; if not, write to the Free Software
  Foundation, Inc., 51 Franklin St, Fifth Floor, Boston, MA  02110-1301  USA
*/
#include <avr/pgmspace.h>
#include <util/atomic.h>
#include <stdio.h>
#include <stdlib.h>
#include <ctype.h>
#include <stdbool.h>
#include "../lib/parse.h"
#include "../lib/timers.h"
#include "../lib/pin_num.h"
#include "../lib/pins_board.h"
#include "digital.h"

#define SERIAL_PRINT_DELAY_MILSEC 10000
static unsigned long serial_print_started_at;

// pin number must be valid in arg[0] from parse
void echo_digital_pin_in_json_rply(void)
{
    if (atoi(arg[0]) == 10) 
    {
        printf_P(PSTR("PB2"));
    }
    if (atoi(arg[0]) == 11) 
    {
        printf_P(PSTR("PB3"));
    }
    if (atoi(arg[0]) == 12)
    {
        printf_P(PSTR("PB4"));
    }
    if (atoi(arg[0]) == 13) 
    {
        printf_P(PSTR("PB5"));
    }
    if (atoi(arg[0]) == 14)
    {
        printf_P(PSTR("PC0"));
    }
    if (atoi(arg[0]) == 15)
    {
        printf_P(PSTR("PC1"));
    }
    if (atoi(arg[0]) == 16)
    {
        printf_P(PSTR("PC2"));
    }
    if (atoi(arg[0]) == 17)
    {
        printf_P(PSTR("PC3"));
    }
}

// pinMode( arg[0], arg[1] )
void Mode(void)
{
    if ( (command_done == 10) )
    {
        // check that arg[0] is a digit 
        if ( ( !( isdigit(arg[0][0]) ) ) )
        {
            printf_P(PSTR("{\"err\":\"pModeNaN\"}\r\n"));
            initCommandBuffer();
            return;
        }
        // and arg[0] value is 10|11|12|13|14|15|16|17 
        uint8_t a = atoi(arg[0]);
        if ( ( a < 10) || (a > 17) )
        {
            printf_P(PSTR("{\"err\":\"pModeOutOfRng\"}\r\n"));
            initCommandBuffer();
            return;
        }
        // also arg[1] is not ('INPUT' or 'OUTPUT')
        if ( !( (strcmp_P( arg[1], PSTR("INPUT")) == 0) || (strcmp_P( arg[1], PSTR("OUTPUT")) == 0) ) ) 
        {
            printf_P(PSTR("{\"err\":\"pModeNaMode\"}\r\n"));
            initCommandBuffer();
            return;
        }
        serial_print_started_at = millis();
        if (strcmp_P( arg[1], PSTR("OUTPUT")) == 0 ) 
        {
            pinMode(a, OUTPUT);
        }
        else
        {
            pinMode(a, INPUT);
        }
        
        printf_P(PSTR("{\""));
        command_done = 11;
    }
    else if ( (command_done == 11) )
    {  
        echo_digital_pin_in_json_rply();
        printf_P(PSTR("\":\""));
        command_done = 12;
    }
    else if ( (command_done == 12) )
    {
        printf( arg[1] );
        printf_P(PSTR("\"}\r\n"));
        initCommandBuffer();
    }
    else
    {
        printf_P(PSTR("{\"err\":\"pModeCmdDnWTF\"}\r\n"));
        initCommandBuffer();
    }
}

// digitalWrite( arg[0], arg[1] )
void Write(void)
{
    if ( (command_done == 10) )
    {
        // check that arg[0] is a digit 
        if ( ( !( isdigit(arg[0][0]) ) ) )
        {
            printf_P(PSTR("{\"err\":\"dWrtNaN\"}\r\n"));
            initCommandBuffer();
            return;
        }
        // and arg[0] value is 10|11|12|13|14|15|16|17 
        uint8_t a = atoi(arg[0]);
        if ( ( a < 10) || (a > 17) )
        {
            printf_P(PSTR("{\"err\":\"dWrtOutOfRng\"}\r\n"));
            initCommandBuffer();
            return;
        }
        // also arg[1] is not ('HIGH' or 'LOW')
        if ( !( (strcmp_P( arg[1], PSTR("HIGH")) == 0) || (strcmp_P( arg[1], PSTR("LOW")) == 0) ) ) 
        {
            printf_P(PSTR("{\"err\":\"dWrtNaState\"}\r\n"));
            initCommandBuffer();
            return;
        }
        serial_print_started_at = millis();
        if (strcmp_P( arg[1], PSTR("HIGH")) == 0 ) 
        {
            digitalWrite(a, HIGH);
        }
        else
        {
            digitalWrite(a, LOW);
        }
        
        printf_P(PSTR("{\""));
        command_done = 11;
    }
    else if ( (command_done == 11) )
    {  
        echo_digital_pin_in_json_rply();
        printf_P(PSTR("\":\""));
        command_done = 12;
    }
    else if ( (command_done == 12) )
    {
        uint8_t a = atoi(arg[0]);
        if ( (a > (NUM_DIGITAL_PINS-1)) ) // the badPinCheck will barf at compile time without testing the value ... amazing
        {
            return;
        }
        bool pin = digitalRead(a);
        if (pin)
        {
            printf_P(PSTR("HIGH"));
        }
        else
        {
            printf_P(PSTR("LOW"));
        }
        printf_P(PSTR("\"}\r\n"));
        initCommandBuffer();
    }
    else
    {
        printf_P(PSTR("{\"err\":\"dWrtCmdDnWTF\"}\r\n"));
        initCommandBuffer();
    }
}

// digitalToggle( arg[0] )
void Toggle(void)
{
    if ( (command_done == 10) )
    {
        // check that arg[0] is a digit 
        if ( ( !( isdigit(arg[0][0]) ) ) )
        {
            printf_P(PSTR("{\"err\":\"dTogNaN\"}\r\n"));
            initCommandBuffer();
            return;
        }
        // and arg[0] value is 10|11|12|13|14|15|16|17 
        uint8_t a = atoi(arg[0]);
        if ( ( a < 10) || (a > 17) )
        {
            printf_P(PSTR("{\"err\":\"dTogOutOfRng\"}\r\n"));
            initCommandBuffer();
            return;
        }
        serial_print_started_at = millis();
        digitalToggle(a);
        
        printf_P(PSTR("{\""));
        command_done = 11;
    }
    else if ( (command_done == 11) )
    {  
        echo_digital_pin_in_json_rply();
        printf_P(PSTR("\":\""));
        command_done = 12;
    }
    else if ( (command_done == 12) )
    {
        uint8_t a = atoi(arg[0]);
        if ( (a > (NUM_DIGITAL_PINS-1)) ) // the badPinCheck will barf at compile time without testing the value ... amazing
        {
            return;
        }
        bool pin = digitalRead(a);
        if (pin)
        {
            printf_P(PSTR("HIGH"));
        }
        else
        {
            printf_P(PSTR("LOW"));
        }
        printf_P(PSTR("\"}\r\n"));
        initCommandBuffer();
    }
    else
    {
        printf_P(PSTR("{\"err\":\"dTogCmdDnWTF\"}\r\n"));
        initCommandBuffer();
    }
}

//digitalRead( arg[0] )
void Read(void)
{
    if ( (command_done == 10) )
    {
        // check that arg[0] is a digit 
        if ( ( !( isdigit(arg[0][0]) ) ) )
        {
            printf_P(PSTR("{\"err\":\"dRdNaN\"}\r\n"));
            initCommandBuffer();
            return;
        }
        // and arg[0] value is 10|11|12|13|14|15|16|17 
        uint8_t a = atoi(arg[0]);
        if ( ( a < 10) || (a > 17) )
        {
            printf_P(PSTR("{\"err\":\"dRdOutOfRng\"}\r\n"));
            initCommandBuffer();
            return;
        }
        serial_print_started_at = millis();
        
        printf_P(PSTR("{\""));
        command_done = 11;
    }
    else if ( (command_done == 11) )
    {  
        echo_digital_pin_in_json_rply();
        printf_P(PSTR("\":\""));
        command_done = 12;
    }
    else if ( (command_done == 12) )
    {
        uint8_t a = atoi(arg[0]);
        if ( (a > (NUM_DIGITAL_PINS-1)) ) // the badPinCheck will barf at compile time without testing the value ... amazing
        {
            return;
        }
        bool pin = digitalRead(a);
        if (pin)
        {
            printf_P(PSTR("HIGH"));
        }
        else
        {
            printf_P(PSTR("LOW"));
        }
        printf_P(PSTR("\"}\r\n"));
        initCommandBuffer();
    }
    else
    {
        printf_P(PSTR("{\"err\":\"dRdCmdDnWTF\"}\r\n"));
        initCommandBuffer();
    }
}
