epccs/RPUno/Eeprom/ee.c

/*
ee is a library that has commands to work with the EEPROM. 
Copyright (C) 2019 Ronald Sutherland

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
  You should have received a copy of the GNU Lesser General Public
  License along with this library; if not, write to the Free Software
  Foundation, Inc., 51 Franklin St, Fifth Floor, Boston, MA  02110-1301  USA
*/
#include <avr/pgmspace.h>
#include <util/atomic.h>
#include <avr/eeprom.h> 
#include <stdio.h>
#include <stdlib.h>
#include <ctype.h>
#include <string.h>
#include "../lib/parse.h"
#include "../lib/adc.h"
#include "../lib/timers.h"
#include "ee.h"

static uint32_t ee_mem;

uint8_t ee_read_type(const char * addr, const char * type)
{
    if ( (type == NULL) || (strcmp_P(type, PSTR("UINT8")) ==0) )
    {
        ee_mem =(uint32_t) eeprom_read_byte((uint8_t*)(atoi(addr)) );
        return 1;
    }
    if ( strcmp_P(type, PSTR("UINT16")) == 0 )
    {
        ee_mem =(uint32_t) eeprom_read_word((uint16_t*)(atoi(addr)));
        return 1;
    }
    if ( strcmp_P(type, PSTR("UINT32")) == 0 )
    {
        ee_mem =(uint32_t) eeprom_read_dword((uint32_t*)(atoi(addr)));
        return 1;
    }
    return 0;
}

/* /0/ee? 0..1023, [UINT8|UINT16|UINT32] */
void EEread(void)
{
    if (arg_count > 2)
    {
        printf_P(PSTR("{\"err\":\"EeRdArgCount\"}\r\n"));
        initCommandBuffer();
        return;
    }
    
    if ( (command_done == 10) )
    {
        // check that argument[0] is in the range 0..1023
        if ( ( !( isdigit(arg[0][0]) ) ) || (atoi(arg[0]) < 0) || (atoi(arg[0]) >= EEPROM_SIZE) )
        {
            printf_P(PSTR("{\"err\":\"EeRdMaxAddr %d\"}\r\n"), EEPROM_SIZE);
            initCommandBuffer();
            return;
        }

        if ( arg_count == 1)
        {
            if (arg[1] != NULL)
            {
                printf_P(PSTR("{\"err\":\"ParserBroken\"}\r\n"));
                initCommandBuffer();
                return;
            }
        }

       // check that argument[1] is UINT8|UINT16|UINT32
        if ( ( arg_count == 2 ) && ( !( (strcmp_P(arg[1], PSTR("UINT8")) == 0) || \
                                                    (strcmp_P(arg[1], PSTR("UINT16")) == 0) || \
                                                    (strcmp_P(arg[1], PSTR("UINT32")) == 0) ) ) )
        {
            printf_P(PSTR("{\"err\":\"EeRdTypUINT8|16|32\"}\r\n"));
            initCommandBuffer();
            return;
        }
        
        printf_P(PSTR("{\"EE[%s]\":{"),arg[0]);
        ee_mem = -1;
        command_done = 11;
    }
    else if ( (command_done == 11) )
    {  //  checking if we can use eeprom, or just loop. There is a delay after a write.
        if ( eeprom_is_ready() ) 
        {
            if (!ee_read_type(arg[0], arg[1]))
            {
                printf_P(PSTR("\"err\":\"EeRdCmdDn11WTF\"}}\r\n"));
                initCommandBuffer();
                return;
            }
            command_done = 12;
        }
    }
    else if ( (command_done == 12) )
    {
        printf_P(PSTR("\"r\":\"%lu\"}}\r\n"),ee_mem);
        initCommandBuffer();
    }
    else
    {
        printf_P(PSTR("{\"err\":\"AdcCmdDoneWTF\"}\r\n"));
        initCommandBuffer();
    }
}

/* /0/ee address,value[,type] */
void EEwrite(void)
{
    if ( (command_done == 10) )
    {
        // check that argument[0] is in the range 0..EEPROM_SIZE
        if ( ( !( isdigit(arg[0][0]) ) ) || (atoi(arg[0]) < 0) || (atoi(arg[0]) >= EEPROM_SIZE) )
        {
            printf_P(PSTR("{\"err\":\"EeAddrSize %d\"}\r\n"), EEPROM_SIZE);
            initCommandBuffer();
            return;
        }
        
        // check that argument[1] is a number (it will not overflow a uint32_t)
        if ( !( isdigit(arg[1][0]) ) )
        {
            printf_P(PSTR("{\"err\":\"EeData!=uint8_t\"}\r\n"));
            initCommandBuffer();
            return;
        }
        ee_mem = strtoul(arg[1], (char **)NULL, 10);

        if ( arg_count == 2)
        {
            if (arg[2] != NULL)
            {
                printf_P(PSTR("{\"err\":\"ParserBroken\"}\r\n"));
                initCommandBuffer();
                return;
            }
        }
        
       // check that argument[2] is UINT8|UINT16|UINT32
        if ( ( arg_count == 3 ) && ( !( (strcmp_P(arg[2], PSTR("UINT8")) == 0) || \
                                                    (strcmp_P(arg[2], PSTR("UINT16")) == 0) || \
                                                    (strcmp_P(arg[2], PSTR("UINT32")) == 0) ) ) )
        {
            printf_P(PSTR("{\"err\":\"EeWrTypUINT8|16|32\"}\r\n"));
            initCommandBuffer();
            return;
        }
        
        printf_P(PSTR("{\"EE[%d]\":{"), atoi(arg[0]));
        command_done = 11;
    }
    else if ( (command_done == 11) )
    {  //  check if we can use eeprom, or just loop.
        if ( eeprom_is_ready() ) 
        {
            if ( (arg[2] == NULL) || (strcmp_P(arg[2], PSTR("UINT8")) == 0) )
            {
                uint8_t value = (uint8_t) (ee_mem & 0xFFU);
                printf_P(PSTR("\"byte\":\"%u\","),value);
                eeprom_write_byte( (uint8_t *) (atoi(arg[0])), value);
            }
            if ( strcmp_P(arg[2], PSTR("UINT16")) == 0 )
            {
                uint16_t value = (uint16_t) (ee_mem & 0xFFFFU);
                printf_P(PSTR("\"word\":\"%u\","),value);
                eeprom_write_word( (uint16_t *) (atoi(arg[0])), value);
            }
            if ( strcmp_P(arg[2], PSTR("UINT32")) == 0 )
            {
                printf_P(PSTR("\"dword\":\"%lu\","),ee_mem);
                eeprom_write_dword( (uint32_t *) (atoi(arg[0])), ee_mem);
            }
            command_done = 12;
        }
    }
    else if ( (command_done == 12) )
    {  //  keep checking if we can use eeprom, there is a delay after a write
        if ( eeprom_is_ready() ) 
        {
            if (!ee_read_type(arg[0], arg[2]))
            {
                printf_P(PSTR("{\"err\":\"EeWrCmdDn12WTF\"}\r\n"));
                initCommandBuffer();
                return;
            }
            command_done = 13;
        }
    }
    else if ( (command_done == 13) )
    {
        printf_P(PSTR("\"r\":\"%lu\"}}\r\n"),ee_mem);
        initCommandBuffer();
    }
    else
    {
        printf_P(PSTR("{\"err\":\"AdcCmdDoneWTF\"}\r\n"));
        initCommandBuffer();
    }
}
