epccs/RPUno/Capture/capture.h

#ifndef Capture_H
#define Capture_H

#include "../lib/icp_buf.h"

extern void Count(void);
extern void Capture(void);
extern void Event(void);
extern void InitICP(void);

extern ICP icp1_db;

#endif // Capture_H 
