epccs/RPUno/XcvrTest/main.c

/* 
Transceiver Test
Copyright (C) 2019 Ronald Sutherland

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
You should have received a copy of the GNU General Public License 
along with the Arduino DigitalIO Library.  If not, see
<http://www.gnu.org/licenses/>.
*/ 

#include <avr/pgmspace.h>
#include <util/delay.h>
#include <avr/io.h>
#include "../lib/timers.h"
#include "../lib/uart.h"
#include "../lib/twi.h"
#include "../lib/adc.h"
#include "../lib/rpu_mgr.h"
#include "../lib/pin_num.h"
#include "../lib/pins_board.h"
#include "../Adc/references.h"

#define BLINK_DELAY 1000UL

static unsigned long blink_started_at;
static unsigned long blink_delay;
static char rpu_addr;
static uint8_t passing;
static uint8_t test_mode_clean;
static uint8_t delayed_outputs;
static uint8_t delayed_data[8];

void setup(void) 
{
    // Turn Off Current Sources
    pinMode(CS0_EN,OUTPUT);
    digitalWrite(CS0_EN,LOW); // Red LED
    pinMode(CS1_EN,OUTPUT);
    digitalWrite(CS1_EN,LOW);
    pinMode(CS2_EN,OUTPUT);
    digitalWrite(CS2_EN,LOW);
    pinMode(CS3_EN,OUTPUT);
    digitalWrite(CS3_EN,LOW);
    pinMode(CS_ICP1_EN,OUTPUT);
    digitalWrite(CS_ICP1_EN,LOW); // Green LED
    
    // Turn Off VOUT to shield (e.g. disconnect VIN from shield)
    pinMode(SHLD_VIN_EN,OUTPUT);
    digitalWrite(SHLD_VIN_EN,LOW);

    pinMode(DIO10,OUTPUT);
    digitalWrite(DIO10,LOW);
    pinMode(DIO13,OUTPUT);
    digitalWrite(DIO13,LOW);

    // Initialize Timers, ADC, and clear bootloader, Arduino does these with init() in wiring.c
    initTimers(); //Timer0 Fast PWM mode, Timer1 & Timer2 Phase Correct PWM mode.
    init_ADC_single_conversion(EXTERNAL_AVCC); // warning AREF must not be connected to anything. opt: EXTERNAL_AVCC|INTERNAL_1V1
    init_uart0_after_bootloader(); // bootloader may have the UART setup

    /* Initialize UART, it returns a pointer to FILE so redirect of stdin and stdout works*/
    stdout = stdin = uartstream0_init(BAUD);

    /* Initialize I2C, with the internal pull-up*/
    twi_init(TWI_PULLUP);

    // Enable global interrupts to start TIMER0 and UART
    sei(); 

    blink_started_at = millis();

    rpu_addr = get_Rpu_address();
    blink_delay = BLINK_DELAY;

    // blink fast if a default address from RPU manager not found
    if (rpu_addr == 0)
    {
        rpu_addr = '0';
        blink_delay = BLINK_DELAY/4;
    }
}

void smbus_address(void)
{
    uint8_t smbus_address = 0x2A;
    uint8_t length = 2;
    uint8_t wait = 1;
    uint8_t sendStop = 1;
    uint8_t txBuffer[2] = {0x00,0x00}; //comand 0x00 should Read the mulit-drop bus addr;
    uint8_t twi_returnCode = twi_writeTo(smbus_address, txBuffer, length, wait, sendStop); 
    if (twi_returnCode != 0)
    {
        passing = 0; 
        printf_P(PSTR(">>> SMBus write failed, twi_returnCode: %d\r\n"), twi_returnCode);
    }
    
    // read_i2c_block_data sends a command byte and then a repeated start followed by reading the data 
    uint8_t cmd_length = 1; // one byte command is sent befor read with the read_i2c_block_data
    sendStop = 0; // a repeated start happens after the command byte is sent
    txBuffer[0] = 0x00; //comand 0x00 matches the above write command
    twi_returnCode = twi_writeTo(smbus_address, txBuffer, cmd_length, wait, sendStop); 
    if (twi_returnCode != 0)
    {
        passing = 0; 
        printf_P(PSTR(">>> SMBus read cmd fail, twi_returnCode: %d\r\n"), twi_returnCode);
    }
    uint8_t rxBuffer[2] = {0x00,0x00};
    sendStop = 1;
    uint8_t bytes_read = twi_readFrom(smbus_address, rxBuffer, length, sendStop);
    if ( bytes_read != length )
    {
        passing = 0; 
        printf_P(PSTR(">>> SMBus read missing %d bytes \r\n"), (length-bytes_read) );
    }
    if ( (rxBuffer[0] == 0x0) && (rxBuffer[1] == '1') )
    {
        printf_P(PSTR("SMBUS cmd %d provided address %d from manager\r\n"), rxBuffer[0], rxBuffer[1]);
    } 
    else  
    { 
        passing = 0; 
        printf_P(PSTR(">>> SMBUS wrong addr %d for cmd %d\r\n"), rxBuffer[1], rxBuffer[0]);
    }
}

void i2c_shutdown(void)
{
    uint8_t i2c_address = 0x29;
    uint8_t length = 2;
    uint8_t wait = 1;
    uint8_t sendStop = 0; // use a repeated start after write
    uint8_t txBuffer[2] = {0x05,0x01};
    uint8_t twi_returnCode = twi_writeTo(i2c_address, txBuffer, length, wait, sendStop); 
    if (twi_returnCode != 0)
    {
        passing = 0; 
        printf_P(PSTR(">>> I2C cmd 5 write fail, twi_returnCode: %d\r\n"), twi_returnCode);
        return;
    }
    uint8_t rxBuffer[2] = {0x00,0x00};
    sendStop = 1;
    uint8_t bytes_read = twi_readFrom(i2c_address, rxBuffer, length, sendStop);
    if ( bytes_read != length )
    {
        passing = 0; 
        printf_P(PSTR(">>> I2C read missing %d bytes \r\n"), (length-bytes_read) );
    }
    if ( (txBuffer[0] == rxBuffer[0]) && (txBuffer[1] == rxBuffer[1]) )
    {
        printf_P(PSTR("I2C Shutdown cmd is clean {%d, %d}\r\n"), rxBuffer[0], rxBuffer[1]);
    } 
    else  
    { 
        passing = 0; 
        printf_P(PSTR(">>> I2C Shutdown cmd echo bad {%d, %d}\r\n"), rxBuffer[0], rxBuffer[1]);
    }
}

void i2c_shutdown_detect(void)
{
    uint8_t i2c_address = 0x29;
    uint8_t length = 2;
    uint8_t wait = 1;
    uint8_t sendStop = 0; // use a repeated start after write
    uint8_t txBuffer[2] = {0x04, 0xFF}; //comand 0x04 will return the value 0x01 (0xff is a byte for the ISR to replace)
    uint8_t twi_returnCode = twi_writeTo(i2c_address, txBuffer, length, wait, sendStop);
    if (twi_returnCode != 0)
    {
        passing = 0; 
        printf_P(PSTR(">>> I2C cmd 4 write fail, twi_returnCode: %d\r\n"), twi_returnCode);
    }
    uint8_t rxBuffer[2] = {0x00,0x00};
    sendStop = 1;
    uint8_t bytes_read = twi_readFrom(i2c_address, rxBuffer, length, sendStop);
    if ( bytes_read != length )
    {
        passing = 0; 
        printf_P(PSTR(">>> I2C read missing %d bytes \r\n"), (length-bytes_read) );
    }
    if ( (txBuffer[0] == rxBuffer[0]) && (0x1 == rxBuffer[1]) )
    {
        printf_P(PSTR("I2C Shutdown Detect cmd is clean {%d, %d}\r\n"), rxBuffer[0], rxBuffer[1]);
    } 
    else  
    { 
        passing = 0; 
        printf_P(PSTR(">>> I2C Shutdown Detect cmd echo bad {%d, %d}\r\n"), rxBuffer[0], rxBuffer[1]);
    }
}

void i2c_testmode_start(void)
{
    uint8_t i2c_address = 0x29;
    uint8_t length = 2;
    uint8_t wait = 1;
    uint8_t sendStop = 0; // use a repeated start after write
    uint8_t txBuffer[2] = {0x30, 0x01}; // preserve the trancever control bits
    uint8_t twi_returnCode = twi_writeTo(i2c_address, txBuffer, length, wait, sendStop);
    if (twi_returnCode != 0)
    {
        passing = 0; 
        printf_P(PSTR(">>> I2C cmd 48 write fail, twi_returnCode: %d\r\n"), twi_returnCode);
    }
    uint8_t rxBuffer[2] = {0x00,0x00};
    sendStop = 1;
    uint8_t bytes_read = twi_readFrom(i2c_address, rxBuffer, length, sendStop);
    if ( bytes_read != length )
    {
        passing = 0; 
        printf_P(PSTR(">>> I2C read missing %d bytes \r\n"), (length-bytes_read) );
    }
    if ( (txBuffer[0] == rxBuffer[0]) && (txBuffer[1]  == rxBuffer[1]) )
    {
        test_mode_clean = 1;
        // delay print until the UART can be used
    } 
    else  
    { 
        passing = 0; 
        printf_P(PSTR(">>> I2C Start Test Mode cmd echo bad {%d, %d}\r\n"), rxBuffer[0], rxBuffer[1]);
    }
}

void i2c_testmode_end(void)
{
    uint8_t i2c_address = 0x29;
    uint8_t length = 2;
    uint8_t wait = 1;
    uint8_t sendStop = 0; // use a repeated start after write
    uint8_t txBuffer[2] = {0x31, 0x01}; // recover trancever control bits and report values in data[1] byte
    uint8_t twi_returnCode = twi_writeTo(i2c_address, txBuffer, length, wait, sendStop);
    if ( test_mode_clean )
    {
        printf_P(PSTR("I2C Start Test Mode cmd was clean {48, 1}\r\n"));
        test_mode_clean = 0;
    }
    if (twi_returnCode != 0)
    {
        passing = 0; 
        printf_P(PSTR(">>> I2C cmd 49 write fail, twi_returnCode: %d\r\n"), twi_returnCode);
    }
    uint8_t rxBuffer[2] = {0x00,0x00};
    sendStop = 1;
    uint8_t bytes_read = twi_readFrom(i2c_address, rxBuffer, length, sendStop);
    if ( bytes_read != length )
    {
        passing = 0; 
        printf_P(PSTR(">>> I2C read missing %d bytes \r\n"), (length-bytes_read) );
    }
    if ( (txBuffer[0] == rxBuffer[0]) && (0xD5 == rxBuffer[1]) )
    {
        printf_P(PSTR("I2C End Test Mode hex is Xcvr cntl bits {%d, 0x%X}\r\n"), rxBuffer[0], rxBuffer[1]);
    } 
    else  
    { 
        passing = 0; 
        printf_P(PSTR(">>> I2C problem /w End Test Mode {%d, %d}\r\n"), rxBuffer[0], rxBuffer[1]);
    }
}

void i2c_testmode_test_xcvrbits(uint8_t xcvrbits)
{
    // do not use UART durring testmode
    if ( test_mode_clean )
    {
        uint8_t i2c_address = 0x29;
        uint8_t length = 2;
        uint8_t wait = 1;
        uint8_t sendStop = 0; // use a repeated start after write
        uint8_t txBuffer[2] = {0x32, 0x01};

        uint8_t twi_returnCode = twi_writeTo(i2c_address, txBuffer, length, wait, sendStop);
        if (twi_returnCode != 0)
        {
            passing = 0;
            delayed_outputs |= (1<<4); // >>> I2C cmd 50 write fail, twi_returnCode: %d\r\n
            delayed_data[4] =  twi_returnCode;
        }
        uint8_t rxBuffer[2] = {0x00,0x00};
        sendStop = 1;
        uint8_t bytes_read = twi_readFrom(i2c_address, rxBuffer, length, sendStop);
        if ( bytes_read != length )
        {
            passing = 0; 
            delayed_outputs |= (1<<5); // >>> I2C read missing %d bytes \r\n
            delayed_data[5] =  length-bytes_read;
        }
        if ( (txBuffer[0] == rxBuffer[0]) && (xcvrbits == rxBuffer[1]) )
        { //0xe2 is 0b11100010
            // HOST_nRTS:HOST_nCTS:TX_nRE:TX_DE:DTR_nRE:DTR_DE:RX_nRE:RX_DE
            delayed_outputs |= (1<<6); // Testmode: read  Xcvr cntl bits {50, 0x%X}\r\n
            delayed_data[6] =  rxBuffer[1];
        } 
        else  
        { 
            passing = 0;
            delayed_outputs |= (1<<7); // >>> Xcvr cntl bits should be %x but report was %x
            delayed_data[7] =  rxBuffer[1]; // used with second format output
        }
    }
}

void i2c_testmode_set_xcvrbits(uint8_t xcvrbits)
{
    // do not use UART durring testmode
    if ( test_mode_clean )
    {
        uint8_t i2c_address = 0x29;
        uint8_t length = 2;
        uint8_t wait = 1;
        uint8_t sendStop = 0; // use a repeated start after write
        uint8_t txBuffer[2];
        txBuffer[0] = 0x33;
        txBuffer[1] = xcvrbits;
        uint8_t twi_returnCode = twi_writeTo(i2c_address, txBuffer, length, wait, sendStop);
        if (twi_returnCode != 0)
        {
            passing = 0;
            delayed_outputs |= (1<<0); // >>> I2C cmd 51 write fail, twi_returnCode: %d\r\n
            delayed_data[0] =  twi_returnCode;
        }
        uint8_t rxBuffer[2] = {0x00,0x00};
        sendStop = 1;
        uint8_t bytes_read = twi_readFrom(i2c_address, rxBuffer, length, sendStop);
        if ( bytes_read != length )
        {
            passing = 0; 
            delayed_outputs |= (1<<1); // >>> I2C read missing %d bytes \r\n
            delayed_data[1] =  length-bytes_read;
        }
        if ( (txBuffer[0] == rxBuffer[0]) && (xcvrbits == rxBuffer[1]) )
        { //0xe2 is 0b11100010
            // HOST_nRTS:HOST_nCTS:TX_nRE:TX_DE:DTR_nRE:DTR_DE:RX_nRE:RX_DE
            delayed_outputs |= (1<<2); // Testmode: set  Xcvr cntl bits {51, 0x%X}\r\n
            delayed_data[2] =  rxBuffer[1];
        } 
        else  
        { 
            passing = 0;
            delayed_outputs |= (1<<3); // >>> Xcvr cntl bits set as %x but report was %x
            delayed_data[3] =  rxBuffer[1]; // used with second format output
        }
    }
}

void test(void)
{
    // Info from some Predefined Macros
    printf_P(PSTR("RPUpi Transceiver Test date: %s\r\n"), __DATE__);
    printf_P(PSTR("avr-gcc --version: %s\r\n"),__VERSION__);
    
    // I2C is used to read serial bus manager address 
    if (rpu_addr == '1')
    {
        printf_P(PSTR("I2C provided address 0x31 from manager\r\n"));
    } 
    else  
    { 
        passing = 0; 
        printf_P(PSTR(">>> I2C failed, or address not 0x31 from manager\r\n"));
        return;
    }

    // SMBus needs connected to RPUno I2C master for testing, it is for write_i2c_block_data and read_i2c_block_data from
    //  https://git.kernel.org/pub/scm/utils/i2c-tools/i2c-tools.git/tree/py-smbus/smbusmodule.c
    // write_i2c_block_data sends a command byte and data to the slave 
    smbus_address();

    // SPI loopback at R-Pi header. e.g., drive MISO/DIO12 to test MOSI/DIO11.
    // with self test wirring MISO/DIO12 can shunt the current from CS3 to bypass yellow LED D2
    pinMode(MISO,OUTPUT);
    digitalWrite(MISO,HIGH);
    digitalWrite(CS3_EN,LOW);
    // and MOSI/DIO11 can shunt the current from CS0 to bypass red LED D3
    pinMode(MOSI,INPUT);
    digitalWrite(MOSI,LOW); // turn off the weak pullup, the RPUpi board has a 3k pullup resistor 
    digitalWrite(CS0_EN,LOW); // a HIGH would drive the MOSI pin with Self-Test wiring
    digitalWrite(CS1_EN,HIGH); // add bias to R1 so MOSI loopback can be seen
    digitalWrite(CS2_EN,HIGH); // add more bias to R1 so MOSI loopback can be seen
    _delay_ms(50) ; // busy-wait delay
    uint8_t miso_rd = digitalRead(MISO);
    uint8_t mosi_rd = digitalRead(MOSI);
    if (miso_rd && mosi_rd) 
    { 
        printf_P(PSTR("MISO loopback to MOSI == HIGH\r\n"));
    }
    else 
    { 
        passing = 0; 
        printf_P(PSTR(">>> MISO %d did not loopback to MOSI %d\r\n"), miso_rd, mosi_rd);
    }

    digitalWrite(MISO,LOW);
    _delay_ms(50) ; // busy-wait delay
    miso_rd = digitalRead(MISO);
    mosi_rd = digitalRead(MOSI);
    if ( (!miso_rd) && (!mosi_rd) ) 
    { 
        printf_P(PSTR("MISO loopback to MOSI == LOW\r\n"));
    }
    else 
    { 
        passing = 0; 
        printf_P(PSTR(">>> MISO %d did not loopback to MOSI %d\r\n"), miso_rd, mosi_rd);
        printf_P(PSTR(">>> POL pin needs 5V for loopback to work\r\n"));
    }
    digitalWrite(CS1_EN,LOW);
    digitalWrite(CS2_EN,LOW);

    // My R-Pi Shutdown is on BCM6 (pin31) and that loops back into SCK on the test header
    pinMode(SCK,INPUT);
    digitalWrite(SCK,LOW); // turn off the weak pullup, the RPUpi board has a 3k pullup resistor 
    pinMode(DIO15,OUTPUT);
    digitalWrite(DIO15,HIGH); // this will bias icp1 input over the self-test wiring so green D1 can allow digital voltage on SCK
    digitalWrite(CS_ICP1_EN,LOW); // Green LED
    _delay_ms(50) ; // busy-wait delay
    uint8_t sck_rd = digitalRead(SCK);
    if (sck_rd ) 
    { 
        printf_P(PSTR("SCK with Shutdown loopback == HIGH\r\n"));
    }
    else 
    { 
        passing = 0; 
        printf_P(PSTR(">>> Shutdown HIGH did not loopback to SCK %d\r\n"), sck_rd);
    }

    // To cause a shutdown I can send the I2C command 5 with data 1
    // note the RPUno can monitor its input power to verify the R-Pi is in shutdown and turn off power to the shield VIN    
    i2c_shutdown();

    _delay_ms(50) ; // busy-wait delay
    sck_rd = digitalRead(SCK);
    if (!sck_rd) 
    { 
        printf_P(PSTR("SCK with Shutdown loopback == LOW\r\n"));
    }
    else 
    { 
        passing = 0; 
        printf_P(PSTR(">>> Shutdown LOW did not loopback to SCK %d\r\n"), sck_rd);
    }
    pinMode(DIO15,INPUT);
    digitalWrite(DIO15,LOW); 

    // Manager should save the shutdown detected after SHUTDOWN_TIME timer runs (see rpubus_manager_state.h in Remote fw for value)
    _delay_ms(1100) ; // busy-wait delay
    i2c_shutdown_detect();

    // Set test mode which will save trancever control bits HOST_nRTS:HOST_nCTS:TX_nRE:TX_DE:DTR_nRE:DTR_DE:RX_nRE:RX_DE
    test_mode_clean = 0;
    delayed_outputs = 0; // each bit selects a output to print
    printf_P(PSTR("\r\n"));
    printf_P(PSTR("Testmode: default trancever control bits\r\n"));
    i2c_testmode_start();
    init_ADC_single_conversion(INTERNAL_1V1);
    _delay_ms(1000) ; // busy-wait delay for input current measurement
    // check xcvr bits after start of testmode. Note printf is done after end of testmode.
    uint8_t xcvrbits_after_testmode_start = 0xE2;
    i2c_testmode_test_xcvrbits(xcvrbits_after_testmode_start);
    float noload_i = analogRead(PWR_I)*((ref_intern_1v1_uV/1.0E6)/1024.0)/(0.068*50.0);

    // End test mode 
    i2c_testmode_end();
    
    // show the delayed test results now that UART is on-line
    if (delayed_outputs & (1<<4))
    {
        printf_P(PSTR(">>> I2C cmd 50 write fail, twi_returnCode: %d\r\n"), delayed_data[4]);
    }
    if (delayed_outputs & (1<<5))
    {
        printf_P(PSTR(">>> I2C read missing %d bytes \r\n"), delayed_data[5]);
    }
    if (delayed_outputs & (1<<6))
    {
        printf_P(PSTR("Testmode: read  Xcvr cntl bits {50, 0x%X}\r\n"), delayed_data[6]);
    }
    if (delayed_outputs & (1<<7))
    {
        printf_P(PSTR(">>> Xcvr cntl bits should be %x but report was %x\r\n"), xcvrbits_after_testmode_start, delayed_data[7]);
    }
    printf_P(PSTR("PWR_I /w no load using INTERNAL_1V1: %1.3f A\r\n"), noload_i);
    if (noload_i > 0.035) 
    { 
        passing = 0; 
        printf_P(PSTR(">>> no load curr is to high.\r\n"));
    }
    if (noload_i < 0.015) 
    { 
        passing = 0; 
        printf_P(PSTR(">>> no load curr is to low.\r\n"));
    }
    
    // set CTS low and verify it loops back to RTS
    // control bits  HOST_nRTS:HOST_nCTS:TX_nRE:TX_DE:DTR_nRE:DTR_DE:RX_nRE:RX_DE
    test_mode_clean = 0;
    delayed_outputs = 0; // each bit selects a output to print
    printf_P(PSTR("\r\n"));
    printf_P(PSTR("Testmode: nCTS loopback to nRTS\r\n"));
    i2c_testmode_start();
    _delay_ms(50) ; // busy-wait delay

    // set nCTS durring testmode and check the loopback on nRTS. Note printf is done after end of testmode.
    uint8_t xcvrbits_change_cts_bit_low = 0xA2; //0b10100010
    i2c_testmode_set_xcvrbits(xcvrbits_change_cts_bit_low);
    uint8_t xcvrbits_cts_loopback_to_rts = 0x22; //0b00100010
    i2c_testmode_test_xcvrbits(xcvrbits_cts_loopback_to_rts);

    // End test mode 
    i2c_testmode_end();
    
    // show the delayed test results now that UART is on-line
    if (delayed_outputs & (1<<0))
    {
        printf_P(PSTR(">>> I2C cmd 51 write fail, twi_returnCode: %d\r\n"), delayed_data[0]);
    }
    if (delayed_outputs & (1<<1))
    {
        printf_P(PSTR(">>> I2C read missing %d bytes \r\n"), delayed_data[1]);
    }
    if (delayed_outputs & (1<<2))
    {
        printf_P(PSTR("Testmode: set  Xcvr cntl bits {51, 0x%X}\r\n"), delayed_data[2]);
    }
    if (delayed_outputs & (1<<3))
    {
        printf_P(PSTR(">>> Xcvr cntl bits should be %x but report was %x\r\n"), xcvrbits_change_cts_bit_low, delayed_data[3]);
    }
    if (delayed_outputs & (1<<4))
    {
        printf_P(PSTR(">>> I2C cmd 50 write fail, twi_returnCode: %d\r\n"), delayed_data[4]);
    }
    if (delayed_outputs & (1<<5))
    {
        printf_P(PSTR(">>> I2C read missing %d bytes \r\n"), delayed_data[5]);
    }
    if (delayed_outputs & (1<<6))
    {
        printf_P(PSTR("Testmode: read  Xcvr cntl bits {50, 0x%X}\r\n"), delayed_data[6]);
    }
    if (delayed_outputs & (1<<7))
    {
        printf_P(PSTR(">>> Xcvr cntl bits should be %x but report was %x\r\n"), xcvrbits_cts_loopback_to_rts, delayed_data[7]);
    }

    // Enable TX driver durring testmode and measure PWR_I.
    test_mode_clean = 0;
    delayed_outputs = 0; // each bit selects a output to print
    printf_P(PSTR("\r\n"));
    printf_P(PSTR("Testmode: Enable TX pair driver\r\n"));
    i2c_testmode_start();
    _delay_ms(50) ; // busy-wait delay
    UCSR0B &= ~( (1<<RXEN0)|(1<<TXEN0) ); // turn off UART 
    pinMode(TX,OUTPUT);
    digitalWrite(TX,LOW); // the TX pair will now be driven and load the transceiver 

    // control bits  HOST_nRTS:HOST_nCTS:TX_nRE:TX_DE:DTR_nRE:DTR_DE:RX_nRE:RX_DE
    // TX_DE drives the twisted pair from this UART, and TX_nRE drives the line to the host (which is not enabled)
    uint8_t xcvrbits_enable_xtde = 0xF2; //0b11110010
    i2c_testmode_set_xcvrbits(xcvrbits_enable_xtde);
    i2c_testmode_test_xcvrbits(xcvrbits_enable_xtde); // to be clear "...set..." does not verify the setting
    _delay_ms(1000) ; // busy-wait delay
    float load_txde_i = analogRead(PWR_I)*((ref_intern_1v1_uV/1.0E6)/1024.0)/(0.068*50.0);

    // End test mode 
    digitalWrite(TX,HIGH); // strong pullup
    _delay_ms(10) ; // busy-wait delay
    pinMode(TX,INPUT); // the TX pair should probably have a weak pullup when UART starts
    UCSR0B |= (1<<RXEN0)|(1<<TXEN0); // turn on UART
    i2c_testmode_end();
    
    // show the delayed test results now that UART is on-line
    if (delayed_outputs & (1<<0))
    {
        printf_P(PSTR(">>> I2C cmd 51 write fail, twi_returnCode: %d\r\n"), delayed_data[0]);
    }
    if (delayed_outputs & (1<<1))
    {
        printf_P(PSTR(">>> I2C read missing %d bytes \r\n"), delayed_data[1]);
    }
    if (delayed_outputs & (1<<2))
    {
        printf_P(PSTR("Testmode: set  Xcvr cntl bits {51, 0x%X}\r\n"), delayed_data[2]);
    }
    if (delayed_outputs & (1<<3))
    {
        printf_P(PSTR(">>> Xcvr cntl bits should be %x but report was %x\r\n"), xcvrbits_enable_xtde, delayed_data[3]);
    }
    if (delayed_outputs & (1<<4))
    {
        printf_P(PSTR(">>> I2C cmd 50 write fail, twi_returnCode: %d\r\n"), delayed_data[4]);
    }
    if (delayed_outputs & (1<<5))
    {
        printf_P(PSTR(">>> I2C read missing %d bytes \r\n"), delayed_data[5]);
    }
    if (delayed_outputs & (1<<6))
    {
        printf_P(PSTR("Testmode: read  Xcvr cntl bits {50, 0x%X}\r\n"), delayed_data[6]);
    }
    if (delayed_outputs & (1<<7))
    {
        printf_P(PSTR(">>> Xcvr cntl bits should be %x but report was %x\r\n"), xcvrbits_enable_xtde, delayed_data[7]);
    }
    printf_P(PSTR("PWR_I /w TX pair load: %1.3f A\r\n"), load_txde_i);
    if (load_txde_i > 0.055) 
    { 
        passing = 0; 
        printf_P(PSTR(">>> TX pair load curr is to high.\r\n"));
    }
    if (load_txde_i < 0.038) 
    { 
        passing = 0; 
        printf_P(PSTR(">>> TX pair load curr is to low.\r\n"));
    }

    // Enable TX and RX driver durring testmode and measure PWR_I.
    test_mode_clean = 0;
    delayed_outputs = 0; // each bit selects a output to print
    printf_P(PSTR("\r\n"));
    printf_P(PSTR("Testmode: Enable TX & RX(loopback) pair drivers\r\n"));
    i2c_testmode_start();
    _delay_ms(50) ; // busy-wait delay
    UCSR0B &= ~( (1<<RXEN0)|(1<<TXEN0) ); // turn off UART 
    pinMode(TX,OUTPUT);
    digitalWrite(TX,LOW); // the TX pair will now be driven and load the transceiver 

    // control bits  HOST_nRTS:HOST_nCTS:TX_nRE:TX_DE:DTR_nRE:DTR_DE:RX_nRE:RX_DE
    // TX_DE drives the TX twisted pair from this UART, and TX_nRE drives the line to the host which is a loopback
    // RX_DE drives the RX twisted pair from the loopback, and RX_nRE drives the line to this RX pair.
    uint8_t xcvrbits_enable_xtrx = 0xD1; //0b11010001
    i2c_testmode_set_xcvrbits(xcvrbits_enable_xtrx);
    i2c_testmode_test_xcvrbits(xcvrbits_enable_xtrx); // to be clear "...set..." does not verify the setting
    _delay_ms(1000) ; // busy-wait delay
    float load_txrx_i = analogRead(PWR_I)*((ref_intern_1v1_uV/1.0E6)/1024.0)/(0.068*50.0);
    uint8_t rx_loopback = digitalRead(RX); 

    // End test mode 
    digitalWrite(TX,HIGH); // strong pullup
    _delay_ms(10) ; // busy-wait delay
    pinMode(TX,INPUT); // the TX pair should probably have a weak pullup when UART starts
    UCSR0B |= (1<<RXEN0)|(1<<TXEN0); // turn on UART
    i2c_testmode_end();
    
    // show the delayed test results now that UART is on-line
    if (delayed_outputs & (1<<0))
    {
        printf_P(PSTR(">>> I2C cmd 51 write fail, twi_returnCode: %d\r\n"), delayed_data[0]);
    }
    if (delayed_outputs & (1<<1))
    {
        printf_P(PSTR(">>> I2C read missing %d bytes \r\n"), delayed_data[1]);
    }
    if (delayed_outputs & (1<<2))
    {
        printf_P(PSTR("Testmode: set  Xcvr cntl bits {51, 0x%X}\r\n"), delayed_data[2]);
    }
    if (delayed_outputs & (1<<3))
    {
        printf_P(PSTR(">>> Xcvr cntl bits should be %x but report was %x\r\n"), xcvrbits_enable_xtrx, delayed_data[3]);
    }
    if (delayed_outputs & (1<<4))
    {
        printf_P(PSTR(">>> I2C cmd 50 write fail, twi_returnCode: %d\r\n"), delayed_data[4]);
    }
    if (delayed_outputs & (1<<5))
    {
        printf_P(PSTR(">>> I2C read missing %d bytes \r\n"), delayed_data[5]);
    }
    if (delayed_outputs & (1<<6))
    {
        printf_P(PSTR("Testmode: read  Xcvr cntl bits {50, 0x%X}\r\n"), delayed_data[6]);
    }
    if (delayed_outputs & (1<<7))
    {
        printf_P(PSTR(">>> Xcvr cntl bits should be %x but report was %x\r\n"), xcvrbits_enable_xtrx, delayed_data[7]);
    }
    printf_P(PSTR("PWR_I /w TX and RX pairs loaded: %1.3f A\r\n"), load_txrx_i);
    if (load_txrx_i > 0.075) 
    { 
        passing = 0; 
        printf_P(PSTR(">>> TX and RX pairs load curr are too high.\r\n"));
    }
    if (load_txrx_i < 0.055) 
    { 
        passing = 0; 
        printf_P(PSTR(">>> TX and RX pairs load curr are too low.\r\n"));
    }
    if (rx_loopback)
    {
        passing = 0;
        printf_P(PSTR(">>> RX loopback should be LOW but was HIGH\r\n"));
    }
    else
    {
        printf_P(PSTR("RX loopback checked\r\n"));
    }

   // Enable DTR driver durring testmode and measure PWR_I.
    test_mode_clean = 0;
    delayed_outputs = 0; // each bit selects a output to print
    printf_P(PSTR("\r\n"));
    printf_P(PSTR("Testmode: Enable DTR pair driver\r\n"));
    i2c_testmode_start();
    _delay_ms(50) ; // busy-wait delay

    // control bits  HOST_nRTS:HOST_nCTS:TX_nRE:TX_DE:DTR_nRE:DTR_DE:RX_nRE:RX_DE
    // everything off except DTR_nRE stays on and DTR_DE is turned on
    // when the i2c commad sees DTR_DE set high it turns off the UART and
    // enables the DTR pair driver then pulls the DTR_TXD line low to load the DTR pair.
    uint8_t xcvrbits_enable_dtr = 0xE6; //0b11100110
    i2c_testmode_set_xcvrbits(xcvrbits_enable_dtr);
    i2c_testmode_test_xcvrbits(xcvrbits_enable_dtr); // to be clear "...set..." does not verify the setting
    _delay_ms(1000) ; // busy-wait delay
    float load_dtr_i = analogRead(PWR_I)*((ref_intern_1v1_uV/1.0E6)/1024.0)/(0.068*50.0);

    // End test mode will setup the DTR_TXD line and enable the manager's UART as it recovers
    i2c_testmode_end();
    
    // show the delayed test results now that UART is on-line
    if (delayed_outputs & (1<<0))
    {
        printf_P(PSTR(">>> I2C cmd 51 write fail, twi_returnCode: %d\r\n"), delayed_data[0]);
    }
    if (delayed_outputs & (1<<1))
    {
        printf_P(PSTR(">>> I2C read missing %d bytes \r\n"), delayed_data[1]);
    }
    if (delayed_outputs & (1<<2))
    {
        printf_P(PSTR("Testmode: set  Xcvr cntl bits {51, 0x%X}\r\n"), delayed_data[2]);
    }
    if (delayed_outputs & (1<<3))
    {
        printf_P(PSTR(">>> Xcvr cntl bits should be %x but report was %x\r\n"), xcvrbits_enable_dtr, delayed_data[3]);
    }
    if (delayed_outputs & (1<<4))
    {
        printf_P(PSTR(">>> I2C cmd 50 write fail, twi_returnCode: %d\r\n"), delayed_data[4]);
    }
    if (delayed_outputs & (1<<5))
    {
        printf_P(PSTR(">>> I2C read missing %d bytes \r\n"), delayed_data[5]);
    }
    if (delayed_outputs & (1<<6))
    {
        printf_P(PSTR("Testmode: read  Xcvr cntl bits {50, 0x%X}\r\n"), delayed_data[6]);
    }
    if (delayed_outputs & (1<<7))
    {
        printf_P(PSTR(">>> Xcvr cntl bits should be %x but report was %x\r\n"), xcvrbits_enable_dtr, delayed_data[7]);
    }
    printf_P(PSTR("PWR_I /w DTR pair load: %1.3f A\r\n"), load_dtr_i);
    if (load_dtr_i > 0.055) 
    { 
        passing = 0; 
        printf_P(PSTR(">>> DTR load curr is to high.\r\n"));
    }
    if (load_dtr_i < 0.038) 
    { 
        passing = 0; 
        printf_P(PSTR(">>> DTR load curr is to low.\r\n"));
    }

    // final test status
    if (passing)
    {
        printf_P(PSTR("[PASS]\r\n"));
    }
    else
    {
        printf_P(PSTR("[FAIL]\r\n"));
    }
    printf_P(PSTR("\r\n\r\n\r\n"));
}

void led_setup_after_test(void)
{
    // Turn Off Curr Sources
    pinMode(CS0_EN,OUTPUT);
    digitalWrite(CS0_EN,LOW); // Red LED
    pinMode(CS1_EN,OUTPUT);
    digitalWrite(CS1_EN,LOW);
    pinMode(CS2_EN,OUTPUT);
    digitalWrite(CS2_EN,LOW);
    pinMode(CS3_EN,OUTPUT);
    digitalWrite(CS3_EN,LOW);
    pinMode(CS_ICP1_EN,OUTPUT);
    digitalWrite(CS_ICP1_EN,LOW); // Green LED

    pinMode(DIO10,INPUT); 
    digitalWrite(DIO10,LOW);
    pinMode(DIO11,INPUT);
    digitalWrite(DIO11,LOW); // is MOSI in hi-z
    pinMode(DIO12,INPUT);
    digitalWrite(DIO12,LOW); // is MISO in hi-z
    pinMode(DIO13,INPUT);
    digitalWrite(DIO13,LOW); // is SCK in hi-z
    pinMode(DIO14,INPUT);
    pinMode(DIO15,INPUT);
    pinMode(DIO16,INPUT);
    pinMode(DIO17,INPUT);
    
    if (passing)
    {
        digitalWrite(CS_ICP1_EN,HIGH); // Green LED
    }
    else
    {
        digitalWrite(CS0_EN,HIGH); // Red LED
    }
}

void blink(void)
{
    unsigned long kRuntime = millis() - blink_started_at;
    if ( kRuntime > blink_delay)
    {
        if (passing)
        {
            digitalToggle(CS_ICP1_EN); // Green LED
        }
        else
        {
            digitalToggle(CS0_EN); // Red LED
        }
        
        // next toggle 
        blink_started_at += blink_delay; 
    }
}

int main(void)
{
    setup(); 
    
    if ( ! LoadAnalogRefFromEEPROM() )
    {
        printf_P(PSTR("{\"err\":\"AdcRefNotInEeprom\"}\r\n"));
        passing = 0;
    }
    else
    {
        passing = 1;
        test();
    }
    led_setup_after_test();
    
    while (1) 
    {
        blink();
    }    
}
